bgdog1/3dPrinterCase/Mainboard Mounts for Pro and XL (Same) V5.x Cases/Mainboard Mount XL V5 - SKR V1.X wMounts.stl

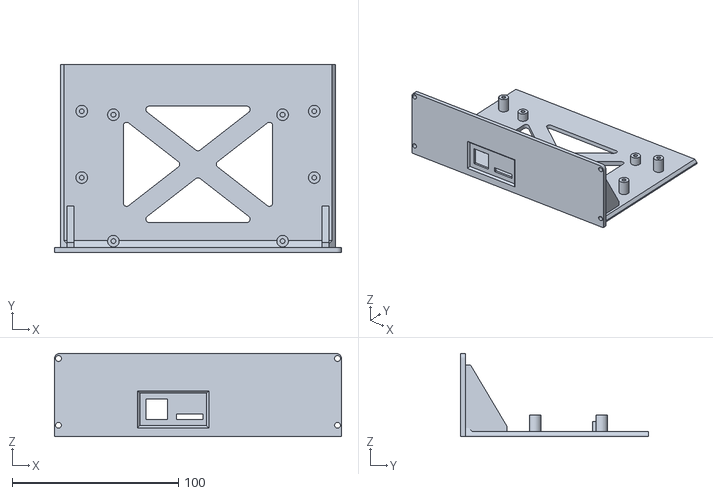
[picture p15: CAD file, 2023-01-29]
Mainboard Mounts for Pro and XL (Same) V5.x Cases/Mainboard Mount XL V5 - SKR V1.X wMounts.stl
172.8 x 113.0 x 50.0
