bgdog1/3dPrinterCase/Mainboard Mounts for V5.x Cases/Mainboard Mount V2 - SKR V1.3 V1.4 V3.0.stl

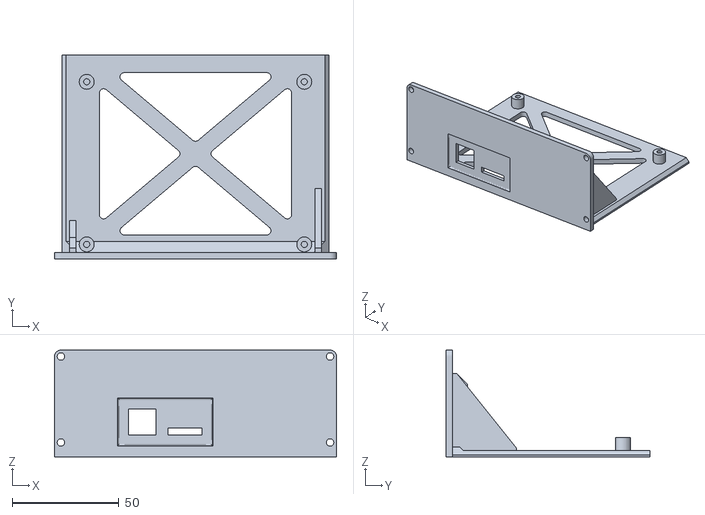
[picture p16: CAD file, 2023-01-29]
Mainboard Mounts for V5.x Cases/Mainboard Mount V2 - SKR V1.3 V1.4 V3.0.stl
132.0 x 95.3 x 50.0
