bgdog1/3dPrinterCase/Rear Mount Ender 3 Case V3.0/E3 Pro Rear Case V5 - Mainboard Lid BTT LOGO.stl

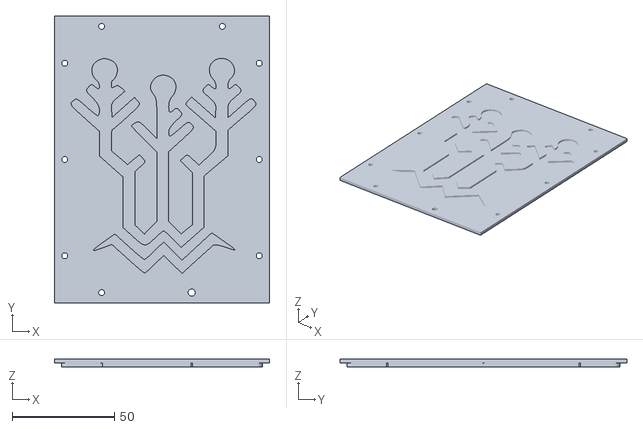
[picture p17: CAD file, 2023-02-08]
Rear Mount Ender 3 Case V3.0/E3 Pro Rear Case V5 - Mainboard Lid BTT LOGO.stl
105.0 x 140.0 x 4.00
