bgdog1/3dPrinterCase/Mainboard Mounts - Case 4.0/Mainboard Mount V4_0 - SKR GTR V1_0.stl

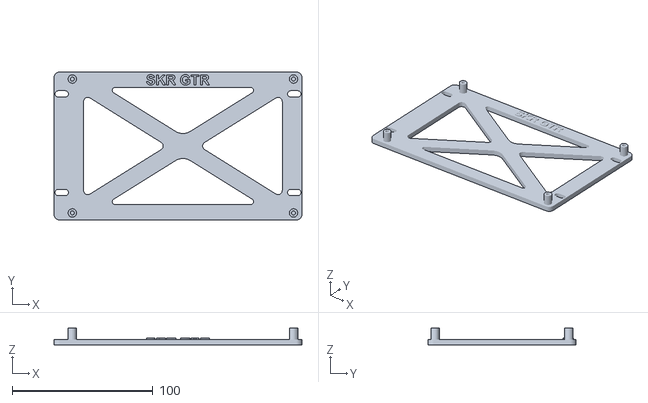
[picture p18: CAD file, 2020-06-05]
Mainboard Mounts - Case 4.0/Mainboard Mount V4_0 - SKR GTR V1_0.stl
176.0 x 105.0 x 12.0
