bgdog1/3dPrinterCase/Mainboard Mounts for Pro and XL (Same) V5.x Cases/Mainboard Mount XL V5 - Duet Wifi.stl

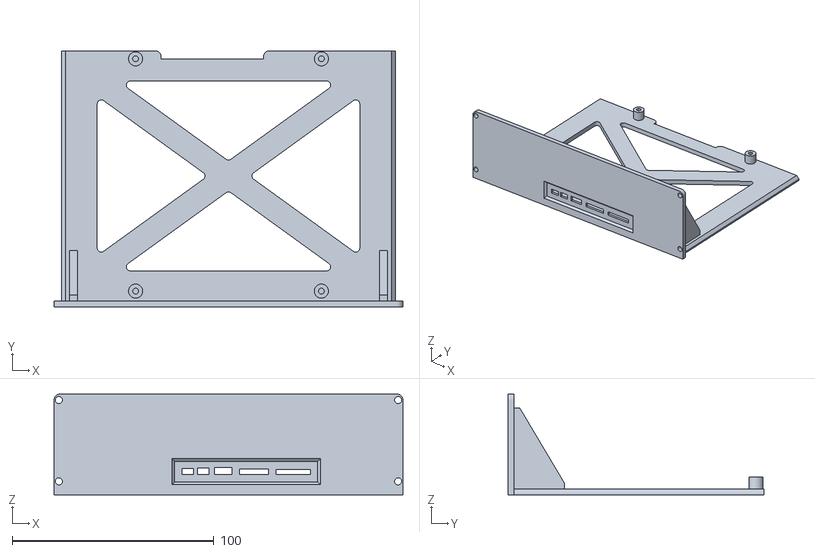
[picture p19: CAD file, 2023-01-29]
Mainboard Mounts for Pro and XL (Same) V5.x Cases/Mainboard Mount XL V5 - Duet Wifi.stl
172.8 x 127.0 x 50.0
