bgdog1/3dPrinterCase/Mainboard Mounts for V5.X Cases/Mainboard Mount V2 - Duet WiFi.stl

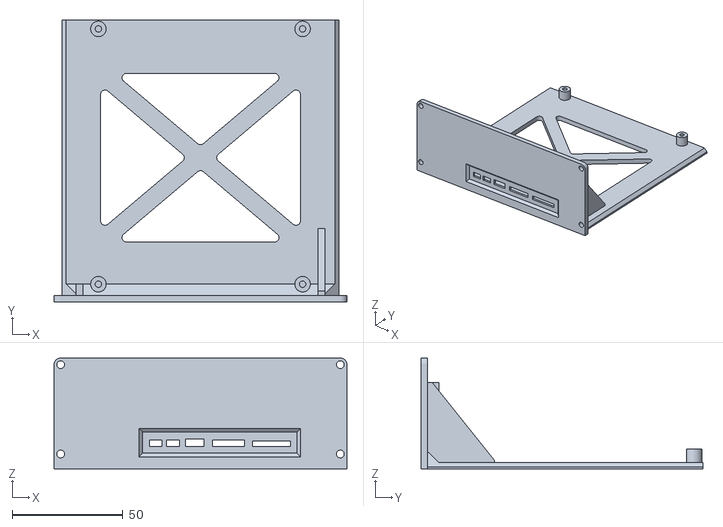
[picture p20: CAD file, 2023-01-29]
Mainboard Mounts for V5.X Cases/Mainboard Mount V2 - Duet WiFi.stl
132.0 x 127.0 x 50.0
