bgdog1/3dPrinterCase/Case - PRO V5.0 - 2 Piece/Main Body Front Pro V5_0 - 2 pc Standard.stl

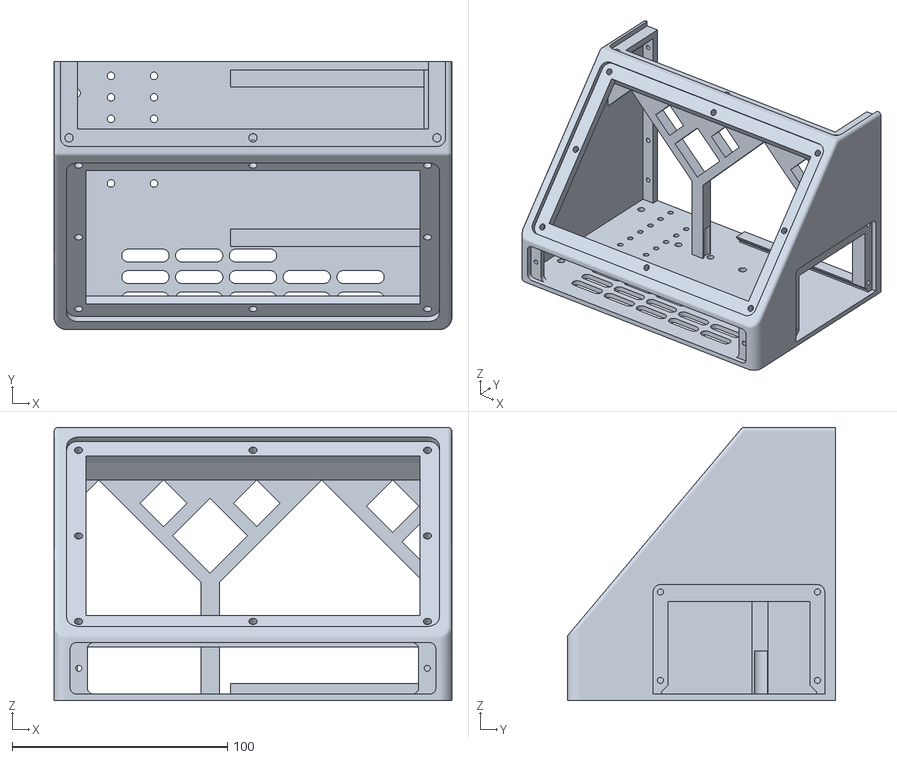
[picture p21: CAD file, 2020-09-07]
Case - PRO V5.0 - 2 Piece/Main Body Front Pro V5_0 - 2 pc Standard.stl
185.0 x 124.8 x 127.0
