bgdog1/3dPrinterCase/Display Mounts - Universal/Display Mount - TFT24V1_1 Main Body SD Accedd.stl

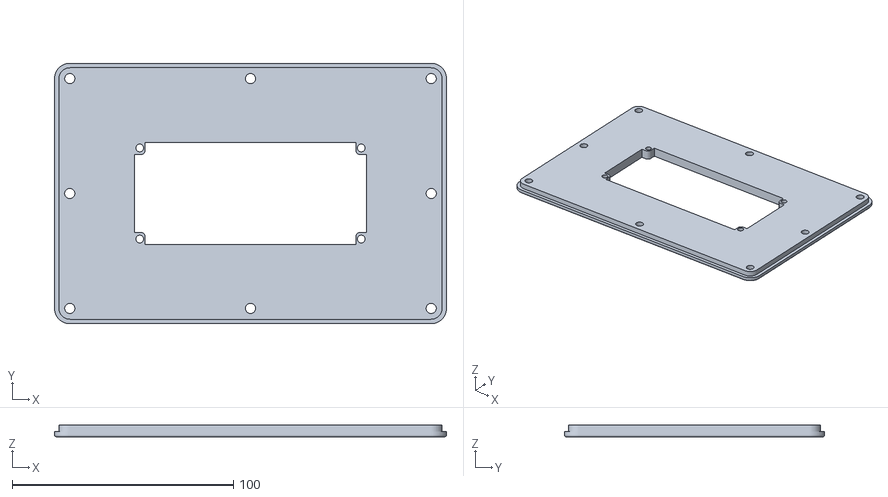
[picture p22: CAD file, 2020-06-08]
Display Mounts - Universal/Display Mount - TFT24V1_1 Main Body SD Accedd.stl
177.1 x 117.6 x 5.40
