bgdog1/3dPrinterCase/Mainboard Mounts for Pro and XL (Same) V5.x Cases/Mainboard Mount XL V5 - SKR GTR V1.0.stl

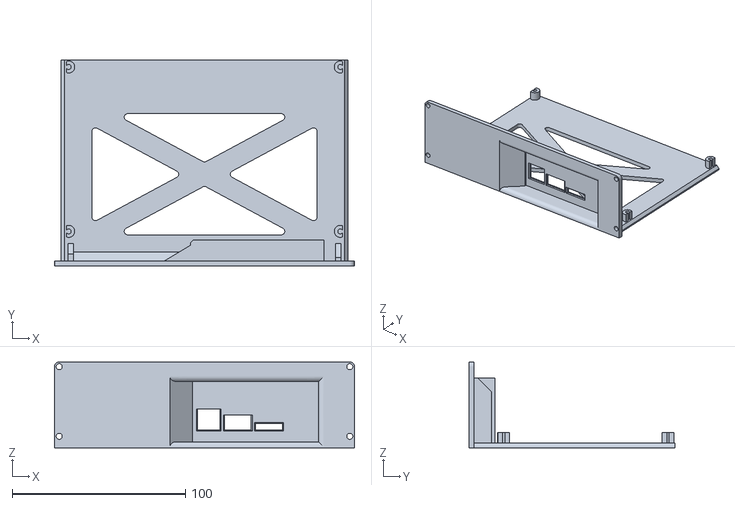
[picture p23: CAD file, 2023-01-29]
Mainboard Mounts for Pro and XL (Same) V5.x Cases/Mainboard Mount XL V5 - SKR GTR V1.0.stl
173.4 x 119.0 x 49.7
