bgdog1/3dPrinterCase/Rear Mount Ender 3 Case V3.0/E3 Pro Rear Case V5 - Mainboard Lid.stl

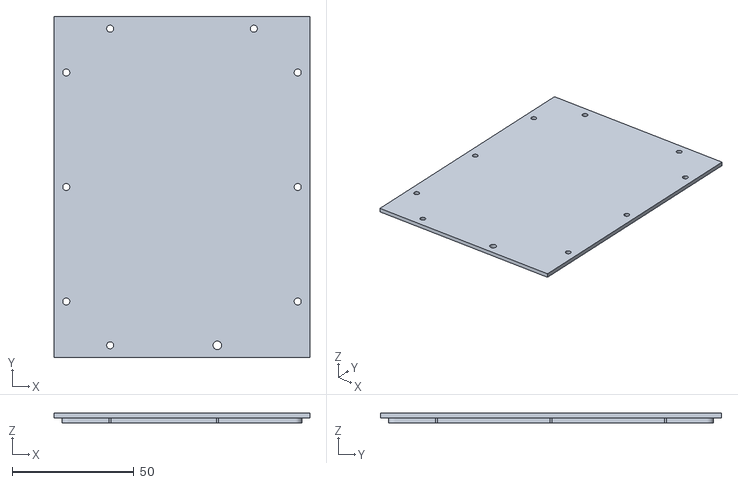
[picture p24: CAD file, 2023-02-08]
Rear Mount Ender 3 Case V3.0/E3 Pro Rear Case V5 - Mainboard Lid.stl
105.0 x 140.0 x 4.00
