bgdog1/3dPrinterCase/Case - PRO V5.0 - 2 Piece/Main Body Rear Pro V5_0 - 2pc Standard.stl

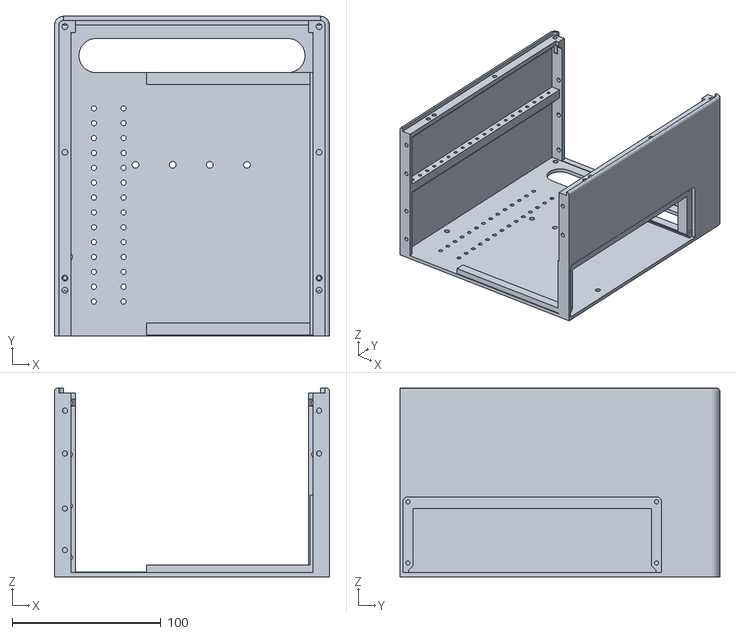
[picture p25: CAD file, 2020-09-07]
Case - PRO V5.0 - 2 Piece/Main Body Rear Pro V5_0 - 2pc Standard.stl
185.0 x 215.0 x 127.0
