bgdog1/3dPrinterCase/Mainboard Mounts for Pro and XL (Same) V5.x Cases/Mainboard Mount XL V5 - SKR Pro V1.1.stl

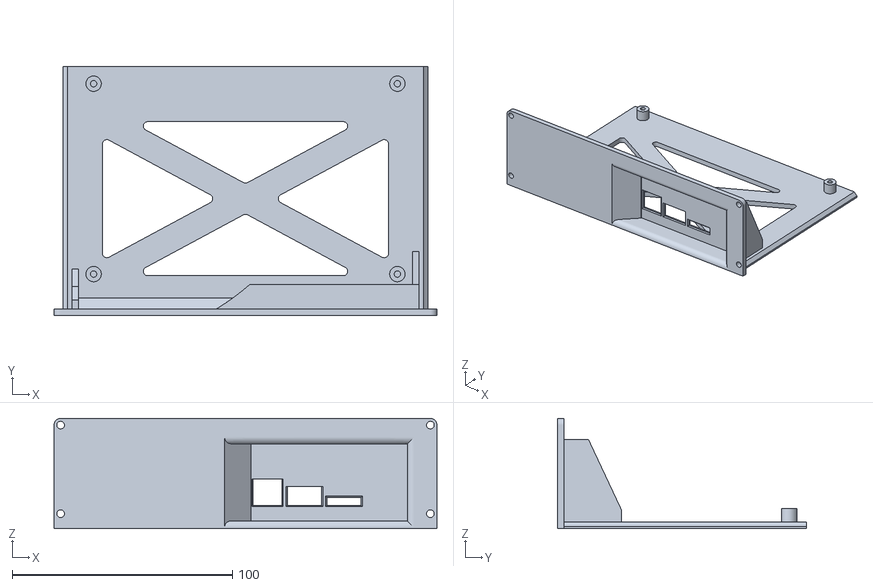
[picture p26: CAD file, 2023-01-29]
Mainboard Mounts for Pro and XL (Same) V5.x Cases/Mainboard Mount XL V5 - SKR Pro V1.1.stl
174.0 x 113.0 x 50.0
