bgdog1/3dPrinterCase/Mainboard Mounts for V5.X Cases/Mainboard Mount V2 - Creality 115_SKR E3.stl

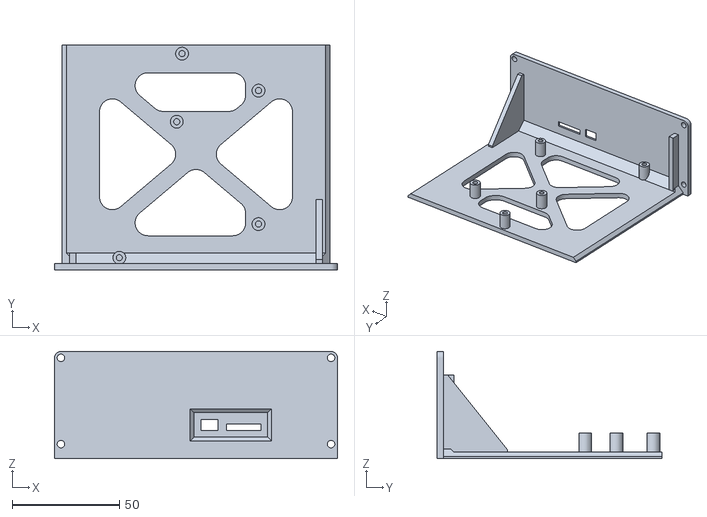
[picture p27: CAD file, 2023-01-29]
Mainboard Mounts for V5.X Cases/Mainboard Mount V2 - Creality 115_SKR E3.stl
132.0 x 105.0 x 50.0
