bgdog1/3dPrinterCase/Mainboard Mounts - Case 4.0/Mainboard Mount V4_0 - Creality 2_X.stl

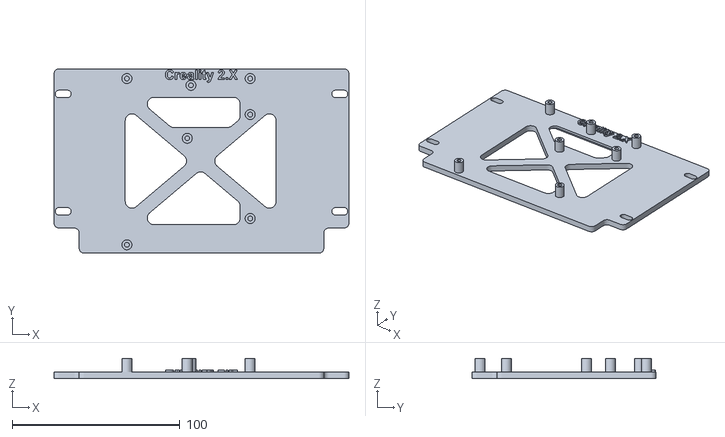
[picture p28: CAD file, 2020-06-01]
Mainboard Mounts - Case 4.0/Mainboard Mount V4_0 - Creality 2_X.stl
176.0 x 110.0 x 12.0
