bgdog1/3dPrinterCase/Mainboard Mounts for Pro and XL (Same) V5.x Cases/Mainboard Mount XL V5 - SKR V1.X wWIFI MOTEXP V1.0.stl

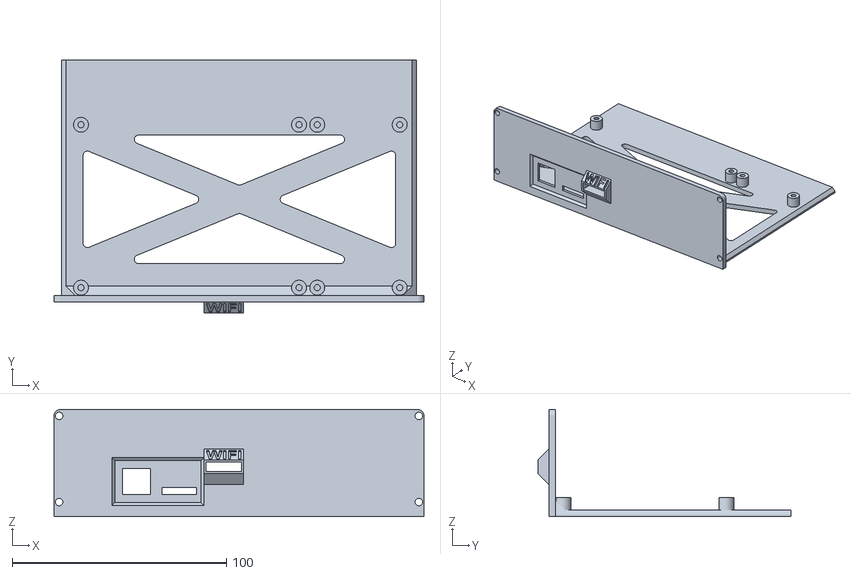
[picture p29: CAD file, 2023-01-29]
Mainboard Mounts for Pro and XL (Same) V5.x Cases/Mainboard Mount XL V5 - SKR V1.X wWIFI MOTEXP V1.0.stl
172.8 x 118.0 x 50.0
