bgdog1/3dPrinterCase/Mainboard Mounts for V5.X Cases/Mainboard Mount V2 - Creality V2_1+.stl

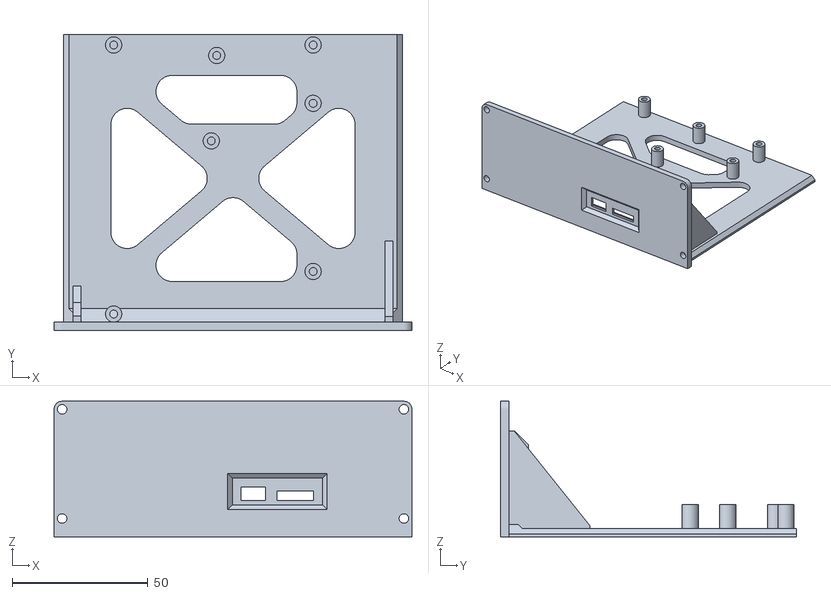
[picture p30: CAD file, 2023-01-29]
Mainboard Mounts for V5.X Cases/Mainboard Mount V2 - Creality V2_1+.stl
132.0 x 109.0 x 50.0
