bgdog1/3dPrinterCase/Rear Mount Ender 3 Case V3.0/E3 Pro Rear Case V5 - 1 Piece Main Body.stl

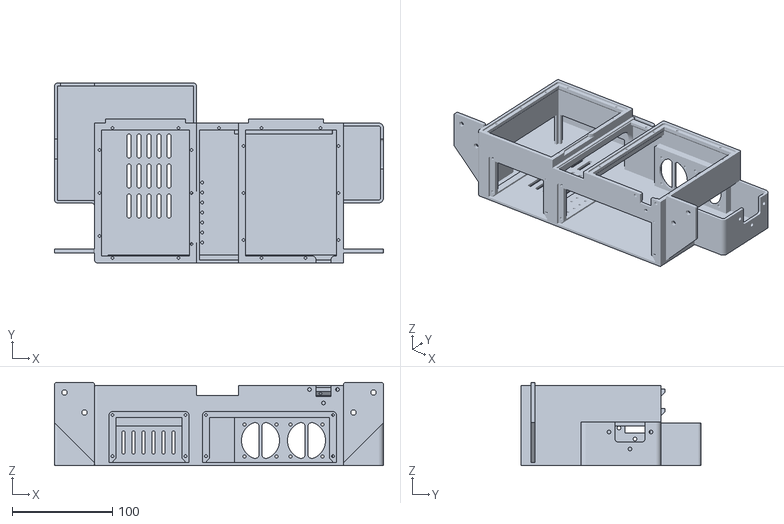
[picture p31: CAD file, 2023-02-08]
Rear Mount Ender 3 Case V3.0/E3 Pro Rear Case V5 - 1 Piece Main Body.stl
329.0 x 180.0 x 83.0
