bgdog1/3dPrinterCase/Mainboard Mounts for V5.X Cases/Mainboard Mount V2 - SKR 1.4 wWIFI.stl

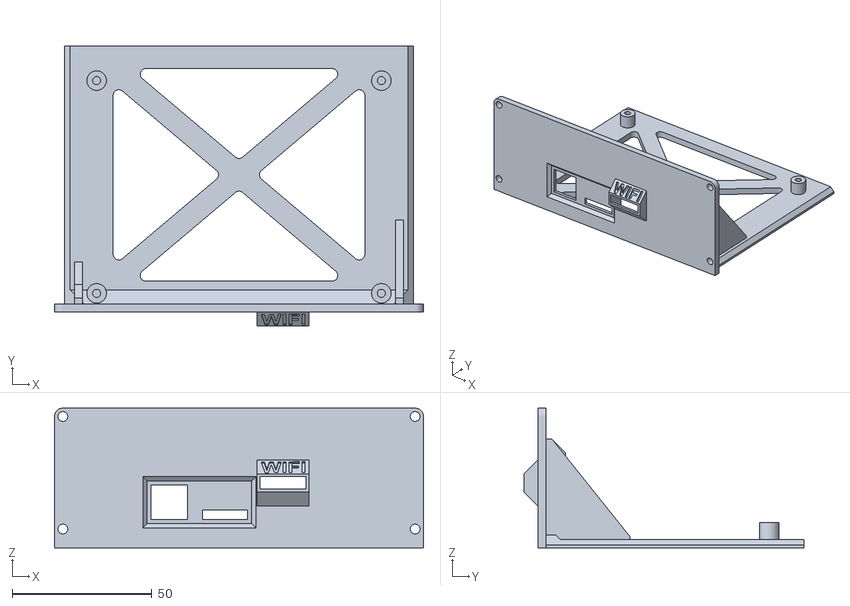
[picture p32: CAD file, 2023-01-29]
Mainboard Mounts for V5.X Cases/Mainboard Mount V2 - SKR 1.4 wWIFI.stl
132.0 x 100.3 x 50.0
