bgdog1/3dPrinterCase/Mainboard Mounts - Case 4.0/Mainboard Mount V4_0 - Blank.stl

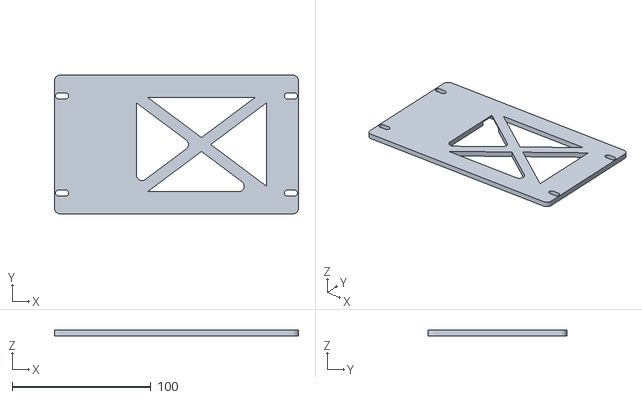
[picture p33: CAD file, 2020-06-01]
Mainboard Mounts - Case 4.0/Mainboard Mount V4_0 - Blank.stl
176.0 x 100.0 x 4.00
