bgdog1/3dPrinterCase/Rear Mount Ender 3 Case V3.0/E3 Pro Rear Case V5 - Mainboard Body.stl

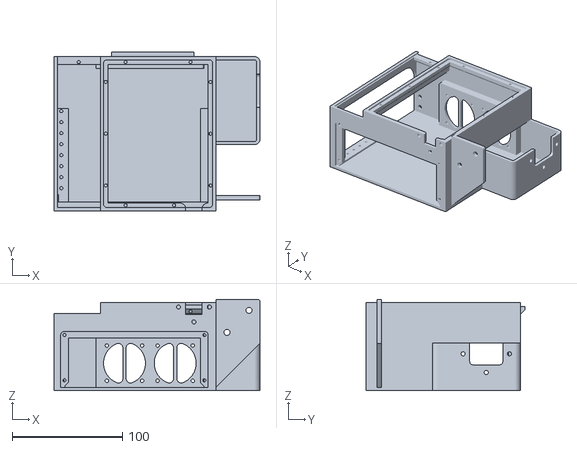
[picture p34: CAD file, 2023-02-07]
Rear Mount Ender 3 Case V3.0/E3 Pro Rear Case V5 - Mainboard Body.stl
187.0 x 144.0 x 83.0
