bgdog1/3dPrinterCase/Mainboard Mounts for V5.X Cases/Mainboard Mount - Creality 115_SKR E3.stl

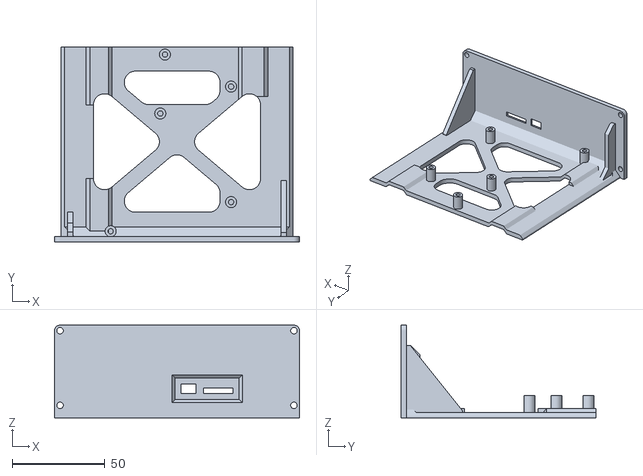
[picture p35: CAD file, 2020-03-22]
Mainboard Mounts for V5.X Cases/Mainboard Mount - Creality 115_SKR E3.stl
132.0 x 105.0 x 50.0
