bgdog1/3dPrinterCase/Mainboard Mounts for V5.X Cases/Mainboard Mount - Creality V2_1+.stl

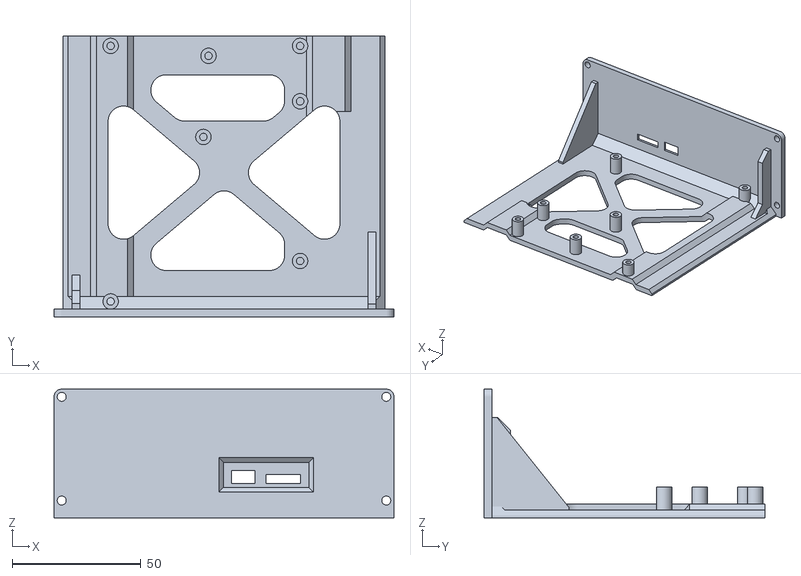
[picture p36: CAD file, 2020-03-22]
Mainboard Mounts for V5.X Cases/Mainboard Mount - Creality V2_1+.stl
132.0 x 109.0 x 50.0
