bgdog1/3dPrinterCase/Buck Converters - Case 3.0 and 5.0/Buck Converter Mount Dbl17x48.stl

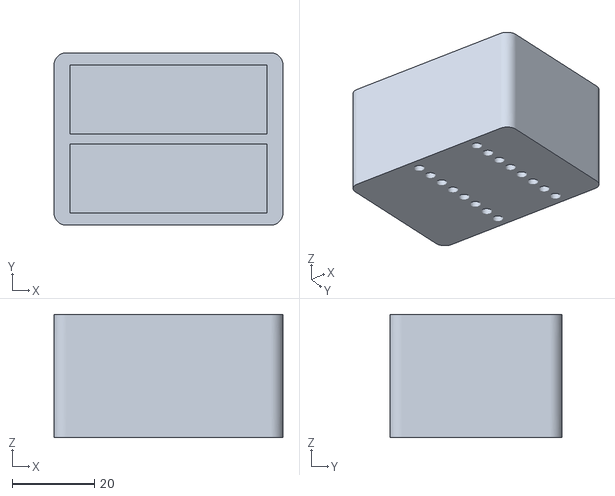
[picture p38: CAD file, 2020-03-22]
Buck Converters - Case 3.0 and 5.0/Buck Converter Mount Dbl17x48.stl
55.8 x 42.0 x 30.0
