bgdog1/3dPrinterCase/Case and Components V4_0 ONLY/RPi Mounts/RPi Mount V4_0 - Horiz_Plain.step

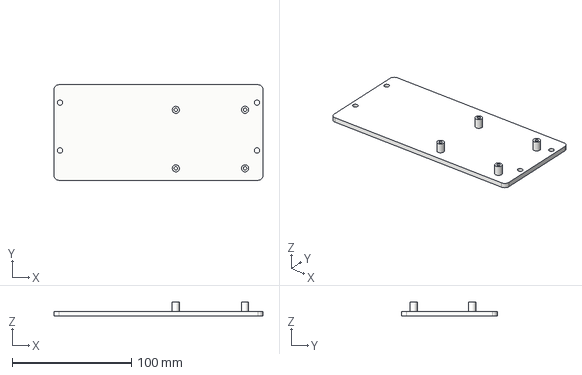
[picture p40: CAD file, 2020-04-26]
Case and Components V4_0 ONLY/RPi Mounts/RPi Mount V4_0 - Horiz_Plain.step
175.0 x 80.0 x 12.0 mm
