bgdog1/3dPrinterCase/CPU Mounts/CPU Mount V2 - Blank.step

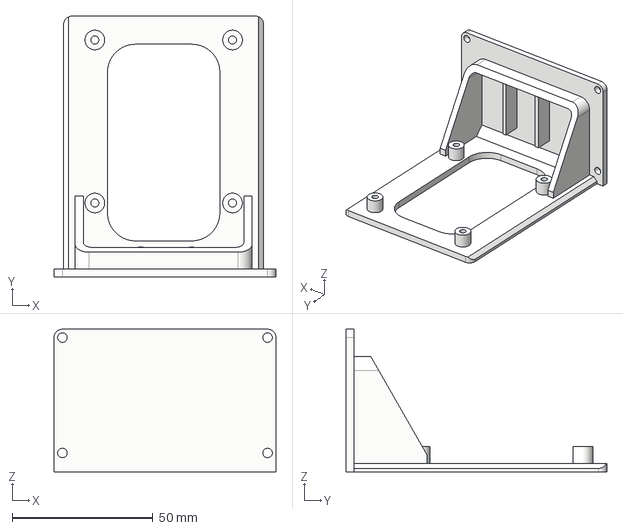
[picture p41: CAD file, 2023-10-05]
CPU Mounts/CPU Mount V2 - Blank.step
79.0 x 92.8 x 50.8 mm
