bgdog1/3dPrinterCase/Display Mounts - Universal/Display Mount - TFT35V20.step

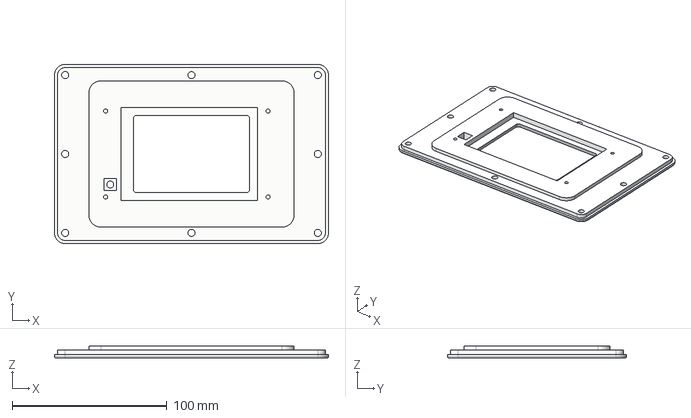
[picture p42: CAD file, 2020-08-09]
Display Mounts - Universal/Display Mount - TFT35V20.step
177.1 x 115.8 x 8.00 mm
