bgdog1/3dPrinterCase/Display Mounts/Display Mount - TFT50V30 Cover.stl

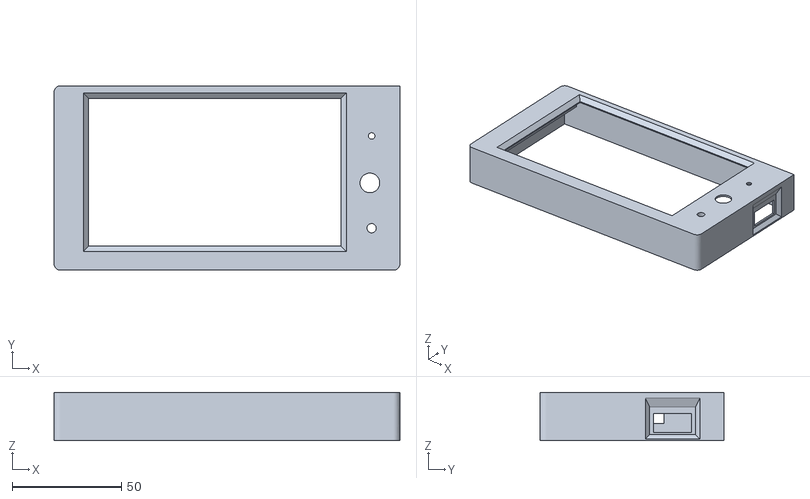
[picture p43: CAD file, 2020-12-30]
Display Mounts/Display Mount - TFT50V30 Cover.stl
158.5 x 84.5 x 22.2
