bgdog1/3dPrinterCase/Fan Hats - Case 3.0 and 5.0/Dual 4020 Fan Hat - Mounting Base.stl

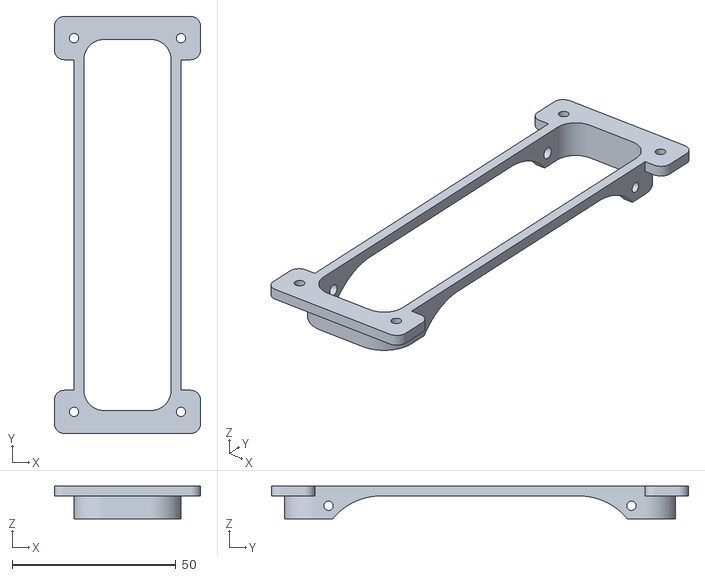
[picture p44: CAD file, 2020-04-03]
Fan Hats - Case 3.0 and 5.0/Dual 4020 Fan Hat - Mounting Base.stl
44.6 x 127.2 x 10.0
