bgdog1/3dPrinterCase/Fan Mounts - Case 3.0 and 5.0/Fan Mount - 4020mm DWT + Bucks + Acc.stl

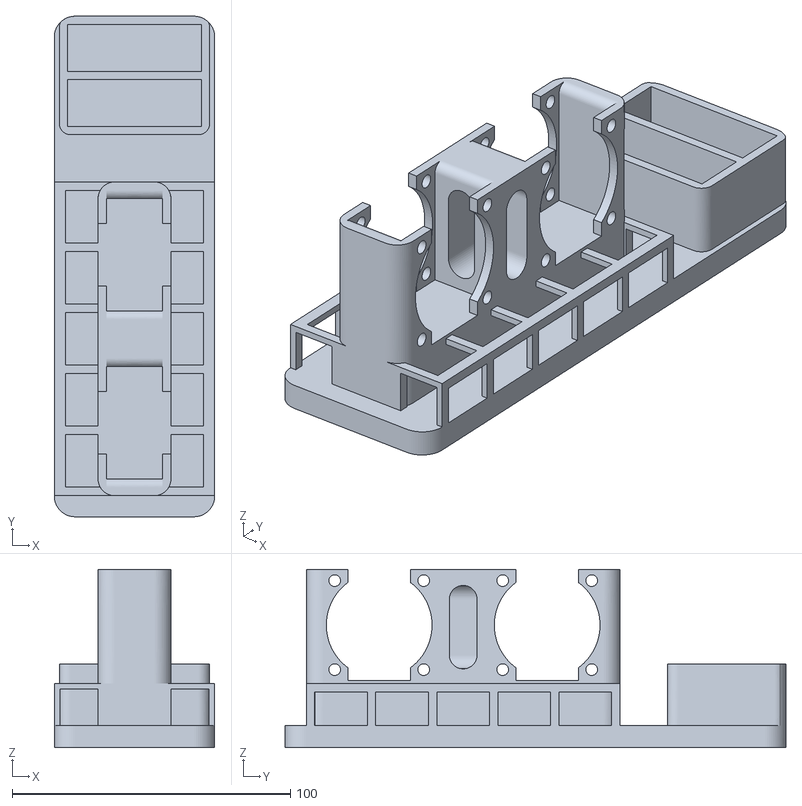
[picture p45: CAD file, 2020-03-30]
Fan Mounts - Case 3.0 and 5.0/Fan Mount - 4020mm DWT + Bucks + Acc.stl
57.7 x 180.0 x 64.0
