bgdog1/3dPrinterCase/Fan Mounts _ Case 3.0 and 5.0/Rear Fan Mount - External 100x25mm Cover.stl

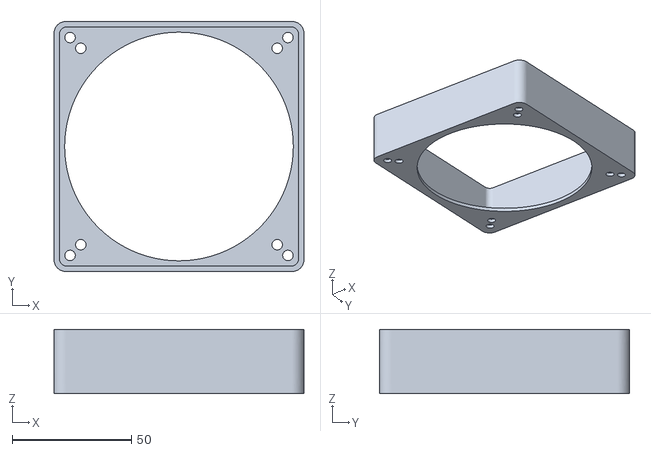
[picture p46: CAD file, 2020-03-28]
Fan Mounts _ Case 3.0 and 5.0/Rear Fan Mount - External 100x25mm Cover.stl
105.0 x 105.0 x 26.9
