bgdog1/3dPrinterCase/Front Covers ALL/Front Vent -  Blank.step

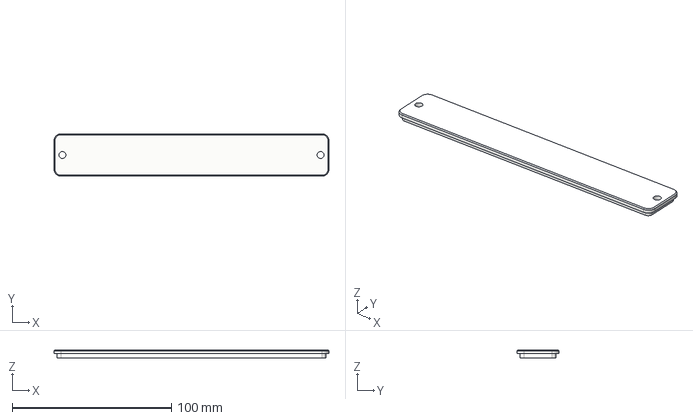
[picture p47: CAD file, 2020-04-05]
Front Covers ALL/Front Vent - Blank.step
172.6 x 26.6 x 5.20 mm
