bgdog1/3dPrinterCase/Front Vents - Universal/Front Vent -  SD_Card.stl

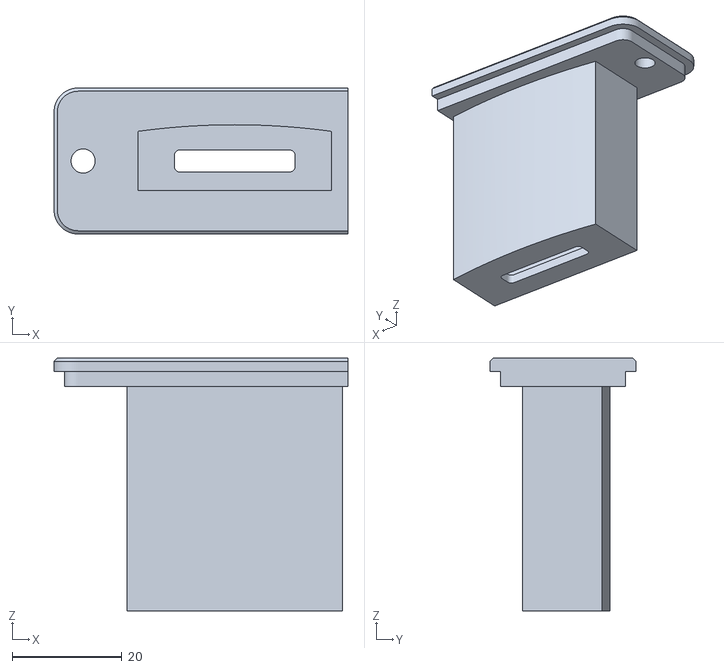
[picture p48: CAD file, 2020-04-26]
Front Vents - Universal/Front Vent - SD_Card.stl
53.5 x 26.6 x 46.0
