bgdog1/3dPrinterCase/Front Vents XL/Front Vent XL - Blank.stl

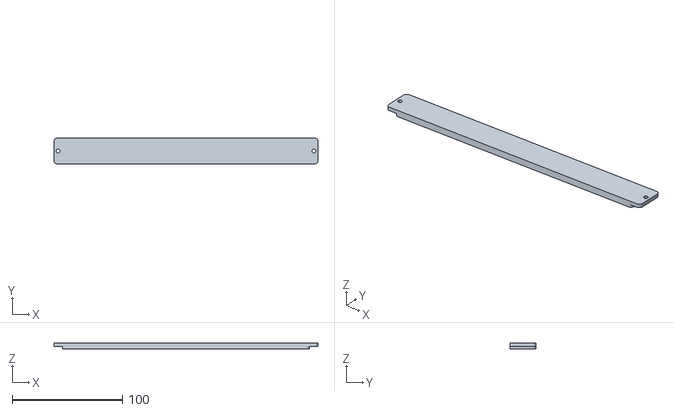
[picture p49: CAD file, 2020-09-06]
Front Vents XL/Front Vent XL - Blank.stl
239.4 x 23.7 x 5.40
