bgdog1/3dPrinterCase/Mainboard Mounts for V5.x Cases/MMV3 CV5 - SKR V3EZ.stl

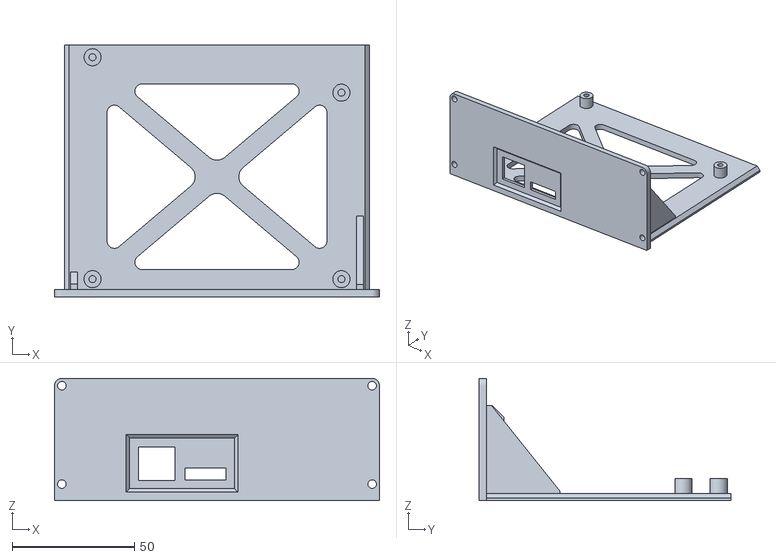
[picture p50: CAD file, 2023-08-20]
Mainboard Mounts for V5.x Cases/MMV3 CV5 - SKR V3EZ.stl
133.0 x 103.0 x 50.0
