bgdog1/3dPrinterCase/Power Panels - Case 3.0/Power Mount Panel Compact - BLANK.stl

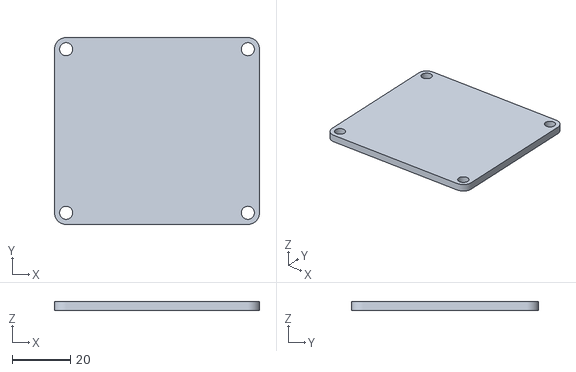
[picture p51: CAD file, 2020-03-22]
Power Panels - Case 3.0/Power Mount Panel Compact - BLANK.stl
70.5 x 64.2 x 3.00
