bgdog1/3dPrinterCase/Rear Fan Cover/Rear Fan External Cover 92mm.stl

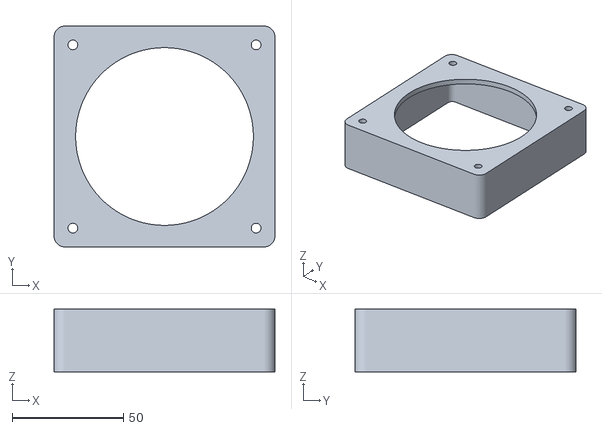
[picture p52: CAD file, 2021-01-09]
Rear Fan Cover/Rear Fan External Cover 92mm.stl
99.5 x 99.5 x 28.2
