bgdog1/3dPrinterCase/Rear Mount Ender 3 Case V3.0/E3 Rear Case V5 - MB Wire Chute.stl

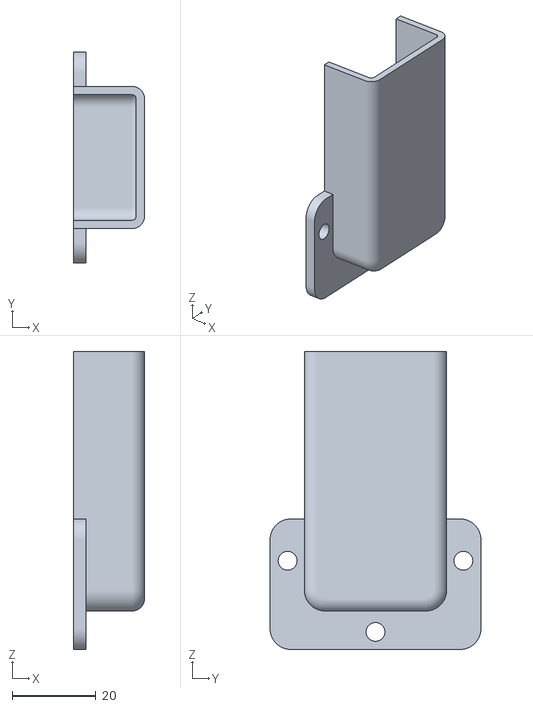
[picture p53: CAD file, 2023-02-08]
Rear Mount Ender 3 Case V3.0/E3 Rear Case V5 - MB Wire Chute.stl
17.0 x 50.4 x 71.2
