bgdog1/3dPrinterCase/Rear Panel XL/Rear Panel - BLANK.stl

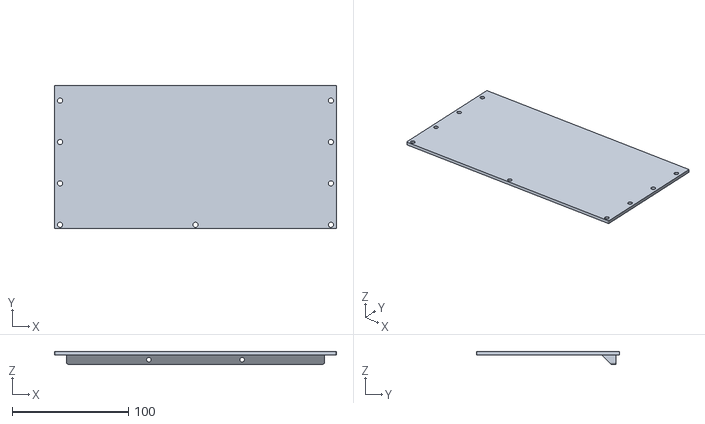
[picture p54: CAD file, 2020-09-12]
Rear Panel XL/Rear Panel - BLANK.stl
242.6 x 123.4 x 11.0
