bgdog1/3dPrinterCase/Rear Panels - Case 4.0 and up/Rear Panel - CR10_100mm_RJ45_2USB.stl

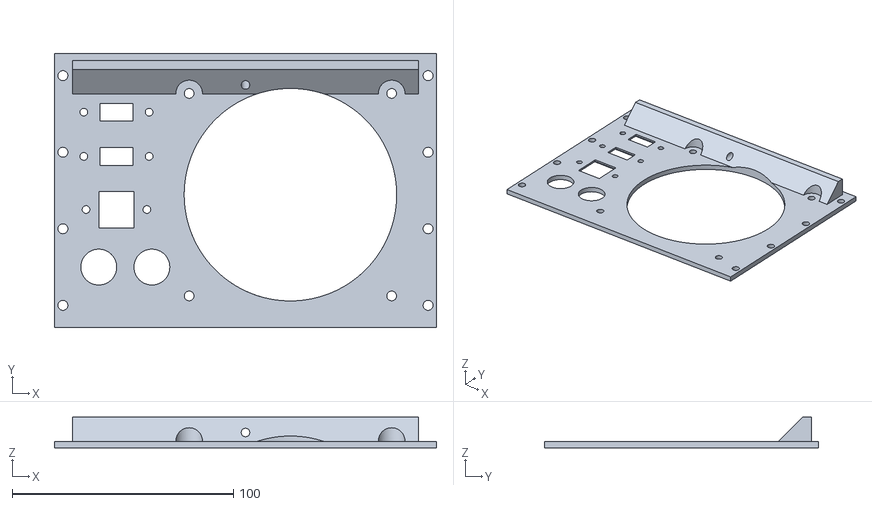
[picture p55: CAD file, 2020-04-26]
Rear Panels - Case 4.0 and up/Rear Panel - CR10_100mm_RJ45_2USB.stl
172.6 x 123.8 x 14.0
