bgdog1/3dPrinterCase/Rear Panels/Rear Panel - 92mmFan and cable holes.stl

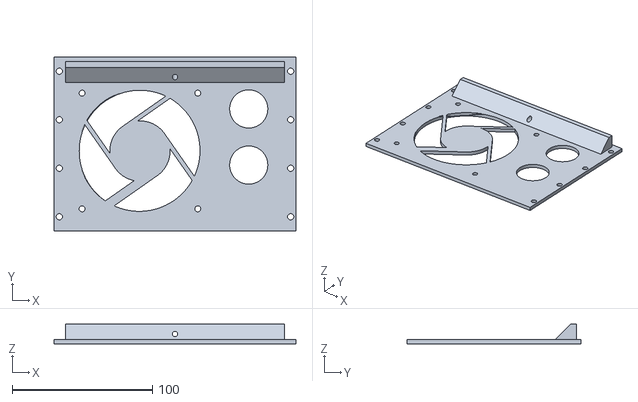
[picture p56: CAD file, 2023-04-07]
Rear Panels/Rear Panel - 92mmFan and cable holes.stl
172.6 x 123.8 x 14.0
