bgdog1/3dPrinterCase/RPi Screen Mounts/TFT 5in RPi Screen Cover.stl

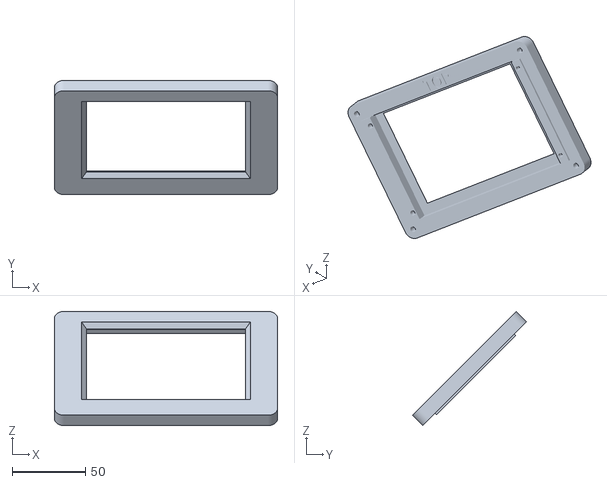
[picture p57: CAD file, 2021-05-05]
RPi Screen Mounts/TFT 5in RPi Screen Cover.stl
152.0 x 77.8 x 77.8
