bgdog1/3dPrinterCase/Side Vent Case 3.0/Side Cover - Blank.stl

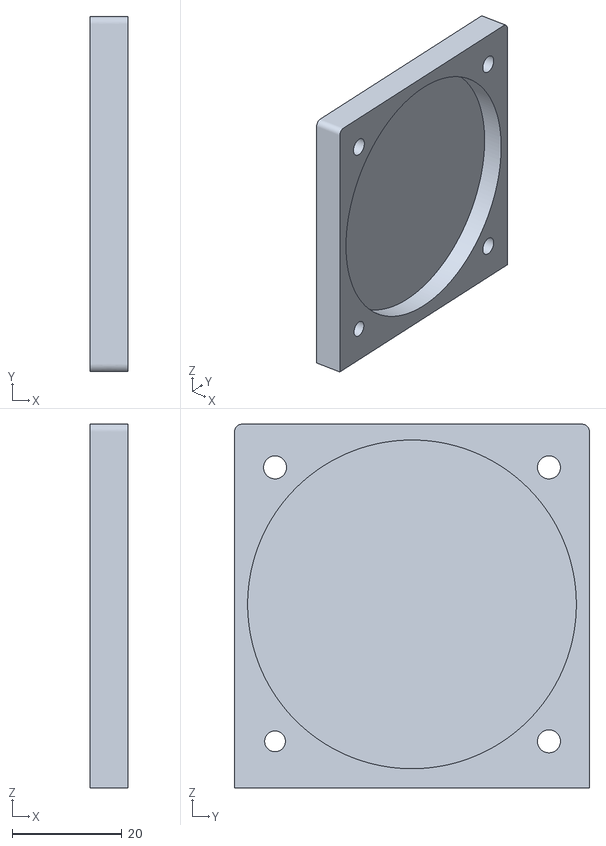
[picture p58: CAD file, 2020-04-05]
Side Vent Case 3.0/Side Cover - Blank.stl
7.00 x 64.8 x 66.4
