bgdog1/3dPrinterCase/Upper Level Mounts - Case 4.0 and up/Upper Level Mount - Wide_2Buck.stl

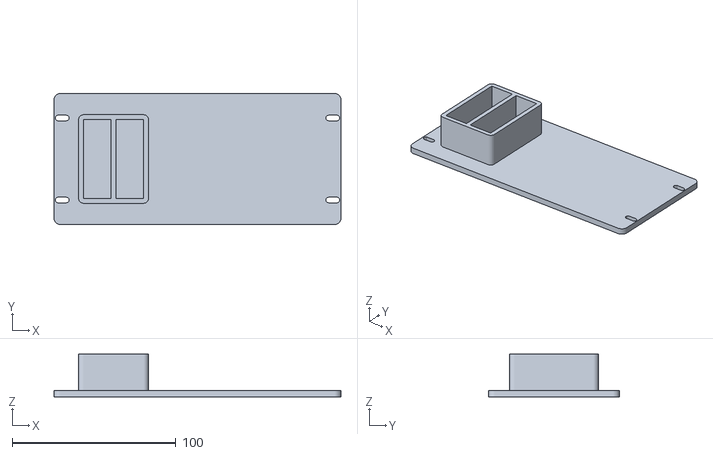
[picture p59: CAD file, 2020-06-04]
Upper Level Mounts - Case 4.0 and up/Upper Level Mount - Wide_2Buck.stl
175.0 x 80.0 x 26.0
