bgdog1/3dPrinterCase/XL and Pro Case Files/Files for Pro V3.0 Only/Power Panel Pro Compact - BLANK.step

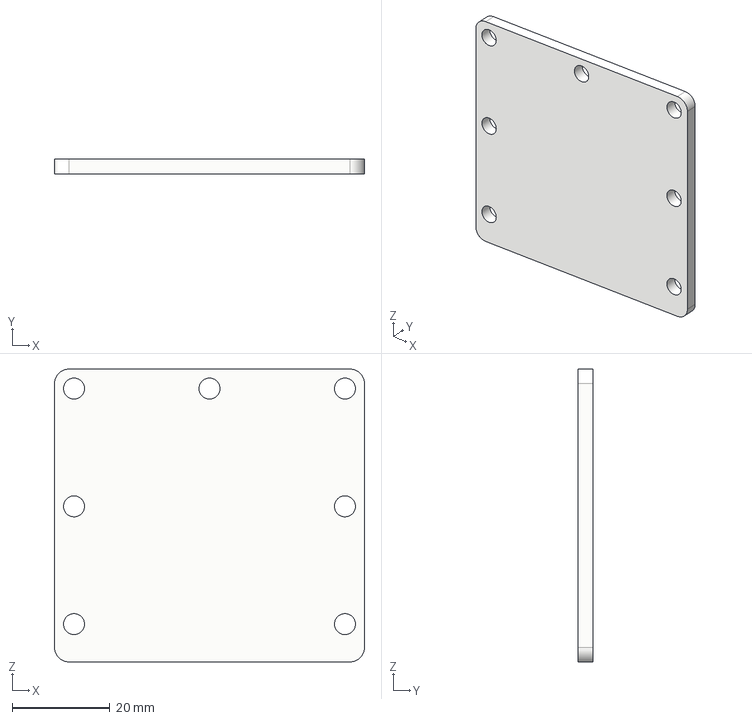
[picture p60: CAD file, 2020-04-22]
XL and Pro Case Files/Files for Pro V3.0 Only/Power Panel Pro Compact - BLANK.step
63.5 x 3.00 x 60.0 mm
