bgdog1/3dPrinterCase/Case - PRO V5.0 - 2 Piece/Base Stand Pro Rear V5_0 Pro_2pc.stl

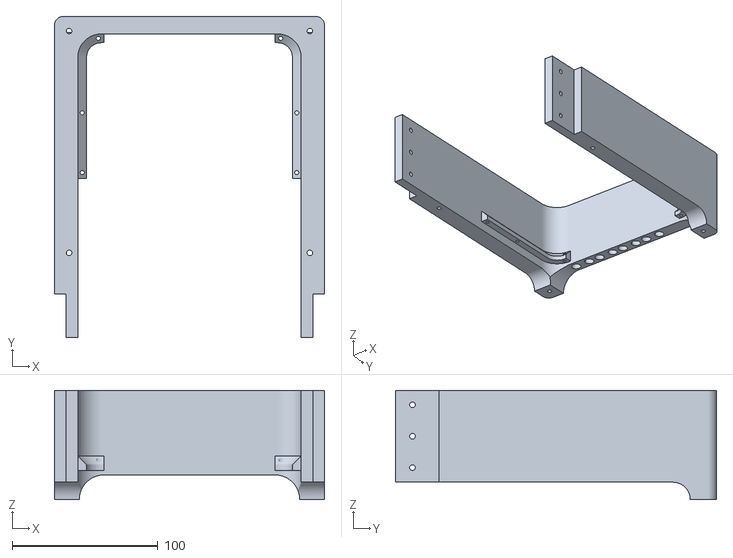
[picture p63: CAD file, 2023-05-02]
Case - PRO V5.0 - 2 Piece/Base Stand Pro Rear V5_0 Pro_2pc.stl
185.0 x 220.0 x 75.0
