bgdog1/3dPrinterCase/Case - PRO V5.0/Base Stand Pro - wSwitch and IEC.stl

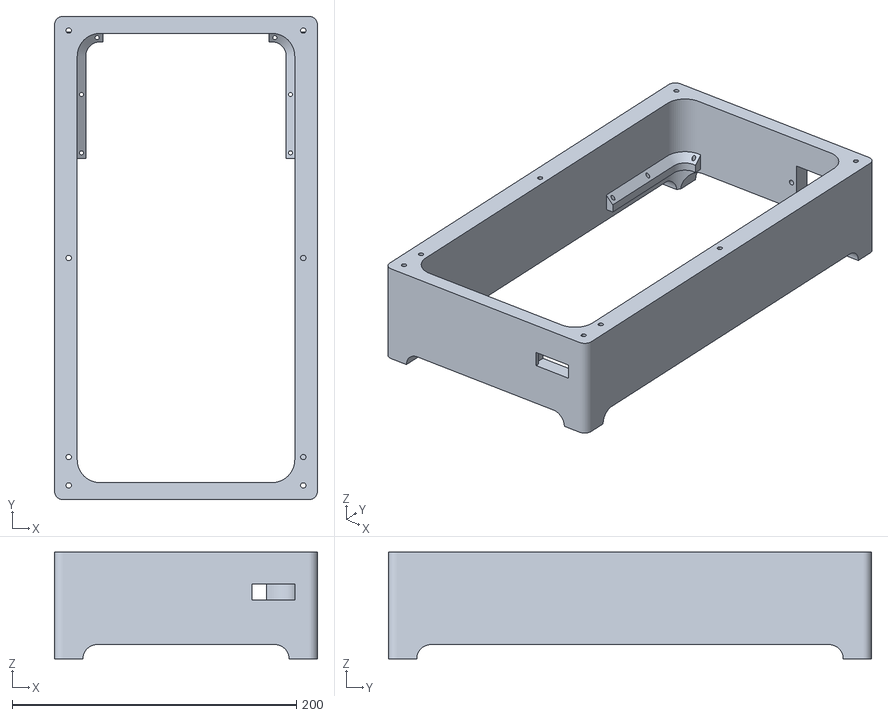
[picture p64: CAD file, 2020-09-22]
Case - PRO V5.0/Base Stand Pro - wSwitch and IEC.stl
185.0 x 340.0 x 75.0
