bgdog1/3dPrinterCase/Case - XL Compact V5.X/Lid XL Compact.stl

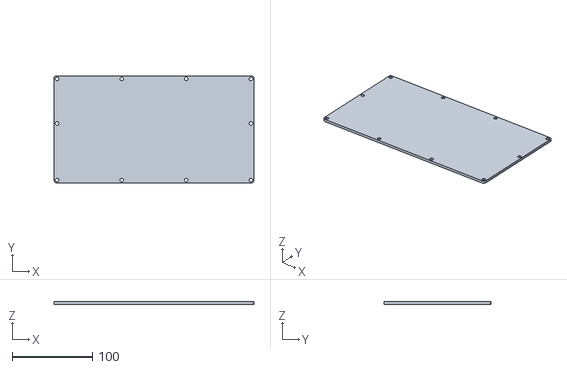
[picture p65: CAD file, 2020-09-06]
Case - XL Compact V5.X/Lid XL Compact.stl
248.5 x 133.1 x 3.20
