bgdog1/3dPrinterCase/Case - XL V5.X/Fan Mount - 4020mm DWT EXTRA Wide.stl

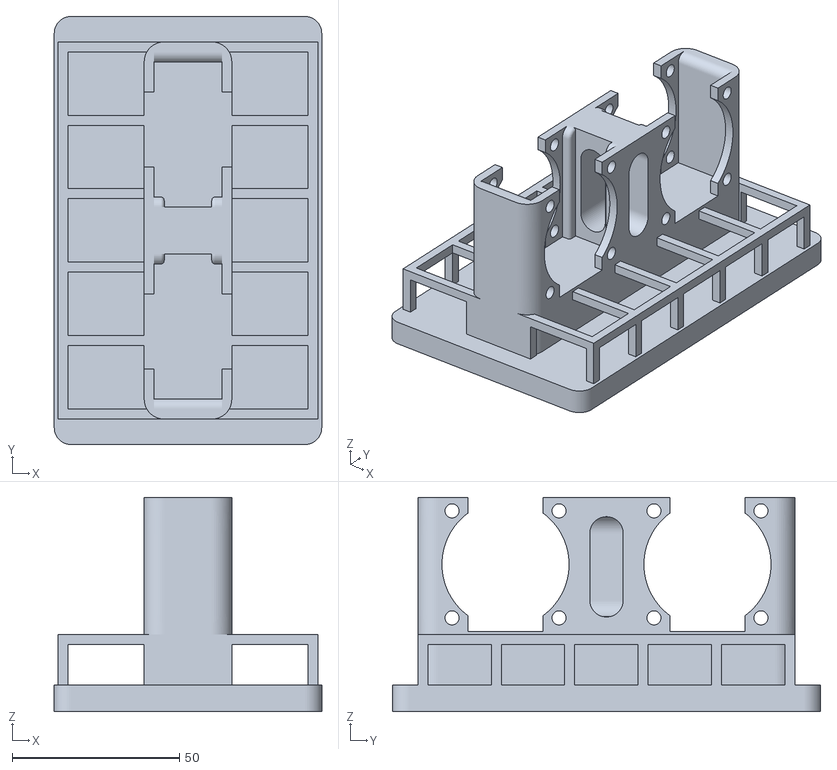
[picture p66: CAD file, 2020-09-22]
Case - XL V5.X/Fan Mount - 4020mm DWT EXTRA Wide.stl
80.0 x 128.0 x 64.0
