bgdog1/3dPrinterCase/CPU Mounts/CPU Mount - RPi 3B+ PRO case.stl

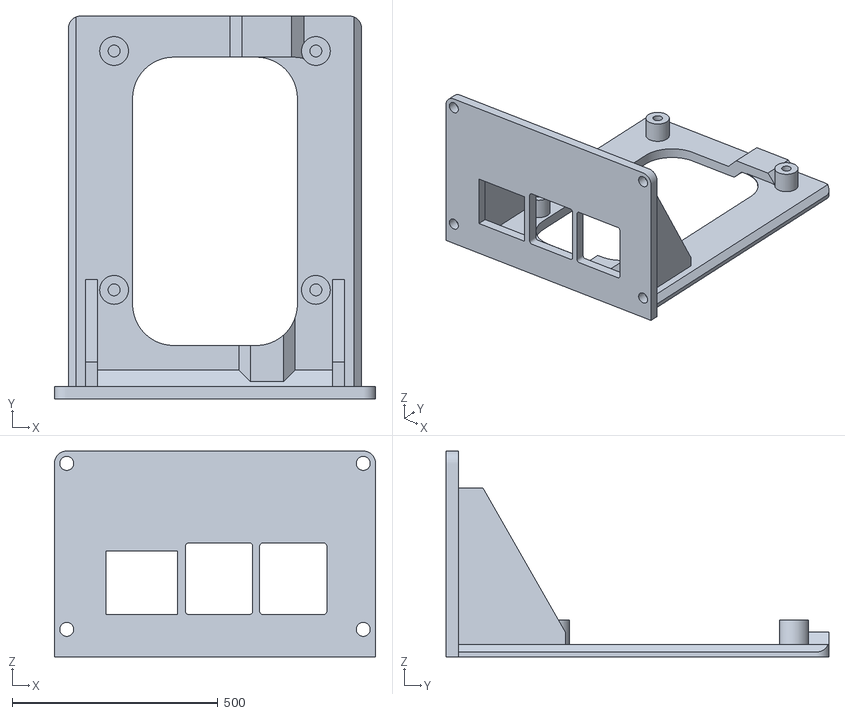
[picture p67: CAD file, 2023-04-07]
CPU Mounts/CPU Mount - RPi 3B+ PRO case.stl
780.0 x 930.0 x 500.0
