bgdog1/3dPrinterCase/Fan Hats - Case 3.0 and 5.0/Dual 4020 Fan Hat - BLANK.stl

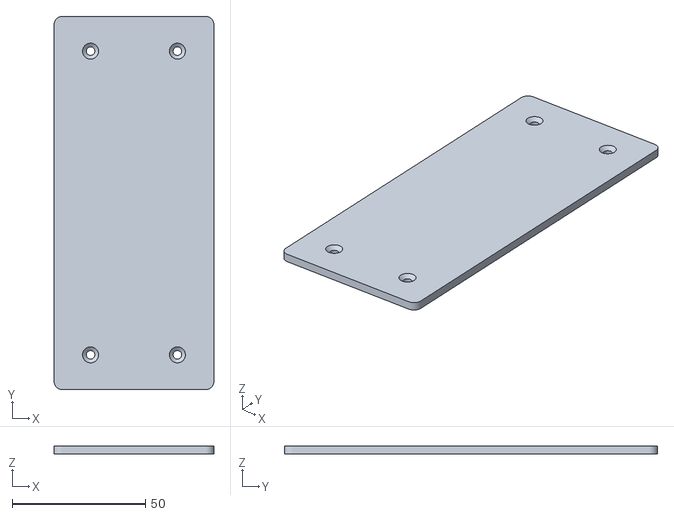
[picture p68: CAD file, 2020-04-03]
Fan Hats - Case 3.0 and 5.0/Dual 4020 Fan Hat - BLANK.stl
60.0 x 140.0 x 3.00
