bgdog1/3dPrinterCase/Fan Mounts - Case 3.0 and 5.0/Fan Mount - Dual 40mm wSgl Cable Tray.stl

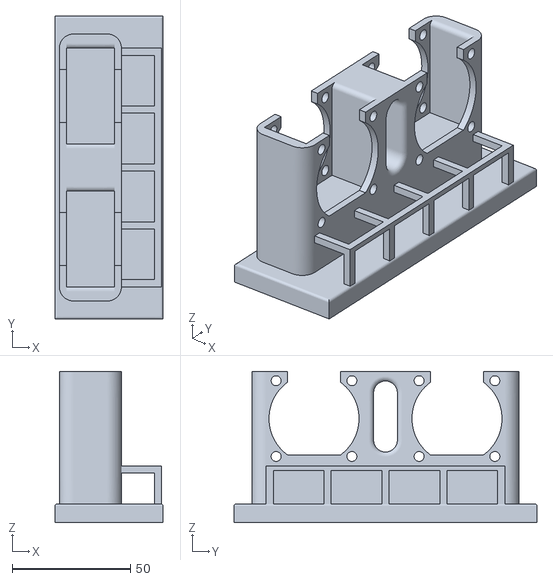
[picture p69: CAD file, 2020-03-29]
Fan Mounts - Case 3.0 and 5.0/Fan Mount - Dual 40mm wSgl Cable Tray.stl
45.7 x 128.0 x 64.0
