bgdog1/3dPrinterCase/Front Vents - Universal/Front Vent -  Hexagon.stl

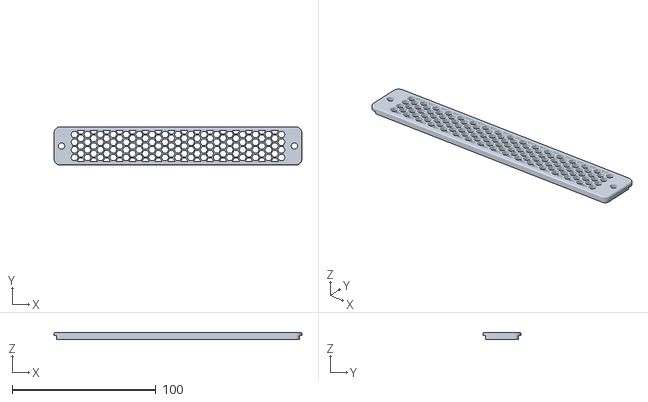
[picture p70: CAD file, 2020-04-05]
Front Vents - Universal/Front Vent - Hexagon.stl
172.6 x 26.6 x 5.20
