bgdog1/3dPrinterCase/Front Vents XL/Front Vent XL - BTT Slots.stl

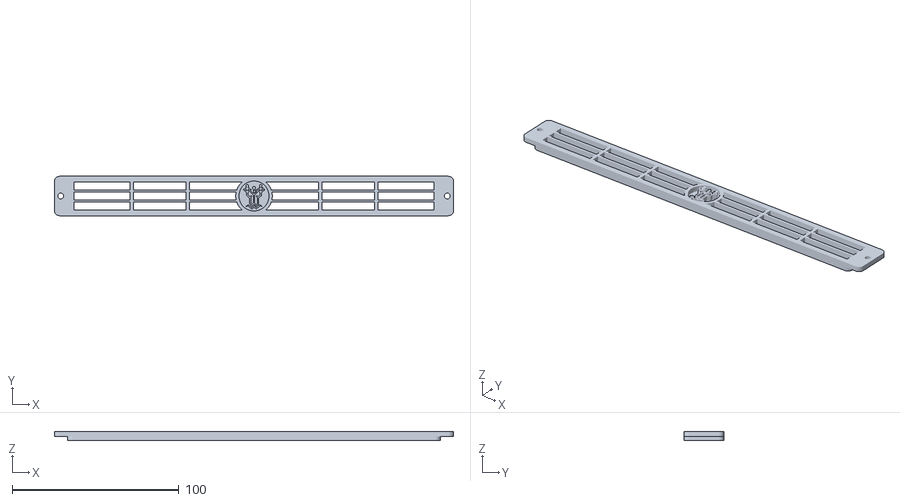
[picture p71: CAD file, 2020-09-06]
Front Vents XL/Front Vent XL - BTT Slots.stl
239.4 x 23.7 x 5.40
