bgdog1/3dPrinterCase/Power Panels - Case 3.0/Power Mount Panel - IEC Connector CR10.stl

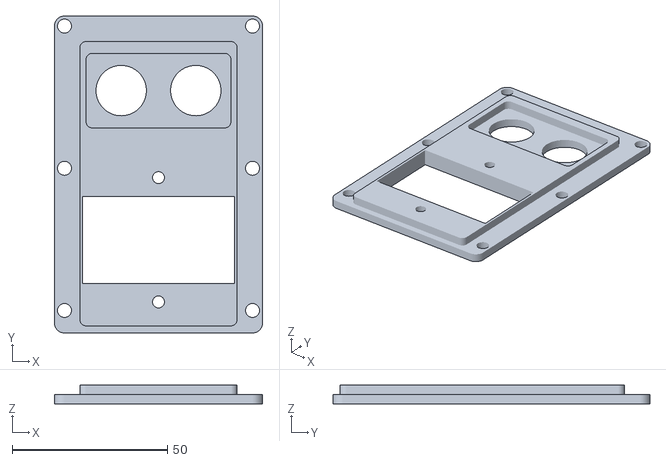
[picture p72: CAD file, 2020-03-22]
Power Panels - Case 3.0/Power Mount Panel - IEC Connector CR10.stl
67.0 x 102.0 x 6.00
