bgdog1/3dPrinterCase/Rear Mount Ender 3 Case V3.0/E3 Rear Case V5 - CPU Side Wire Chute.stl

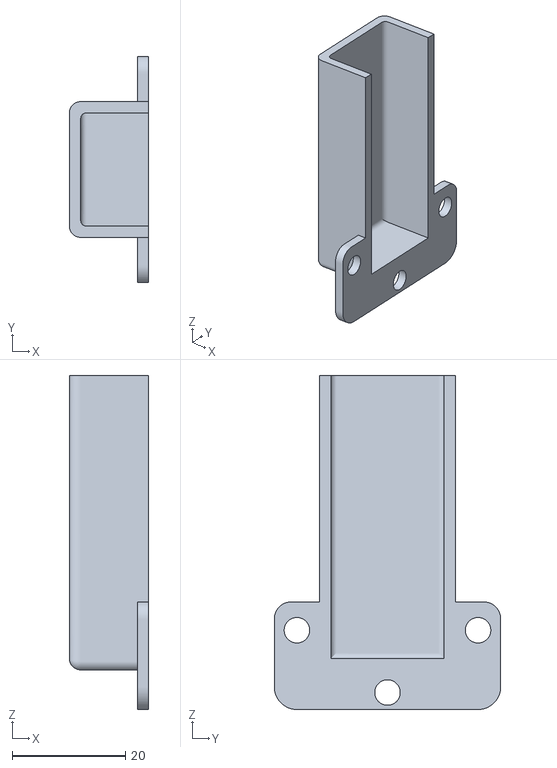
[picture p73: CAD file, 2023-02-08]
Rear Mount Ender 3 Case V3.0/E3 Rear Case V5 - CPU Side Wire Chute.stl
14.0 x 40.0 x 59.0
