bgdog1/3dPrinterCase/Rear Panel XL/Rear Panel - 100mm Fan Left.stl

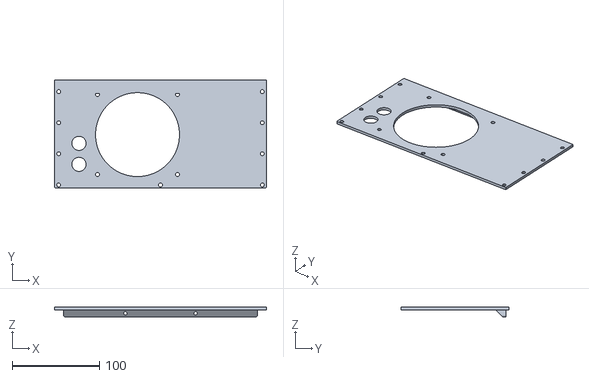
[picture p74: CAD file, 2020-09-12]
Rear Panel XL/Rear Panel - 100mm Fan Left.stl
242.6 x 123.4 x 11.0
