bgdog1/3dPrinterCase/Rear Panels - Case 4.0 and up/Rear Panel - Blank.step

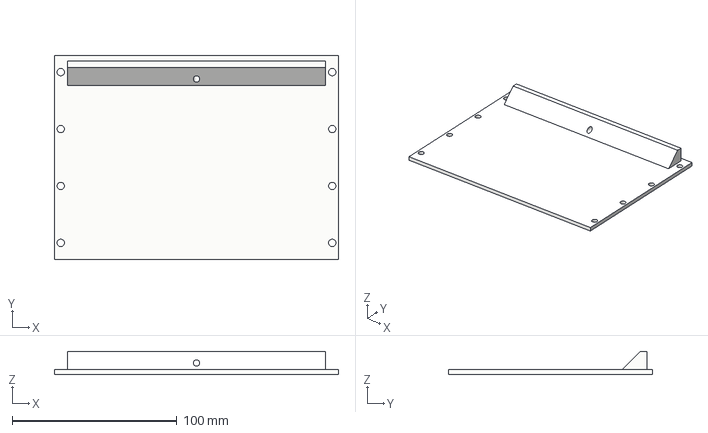
[picture p75: CAD file, 2020-04-24]
Rear Panels - Case 4.0 and up/Rear Panel - Blank.step
172.6 x 123.8 x 14.0 mm
