bgdog1/3dPrinterCase/Rear Panels/Rear Panel - 92mm fan cable and power holes.stl

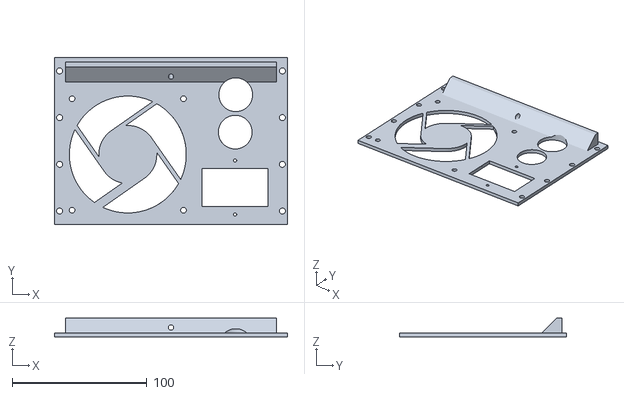
[picture p76: CAD file, 2023-04-07]
Rear Panels/Rear Panel - 92mm fan cable and power holes.stl
172.6 x 123.8 x 14.0
