bgdog1/3dPrinterCase/RPi Screen Mounts/TFT 5in RPi Screen Mount.stl

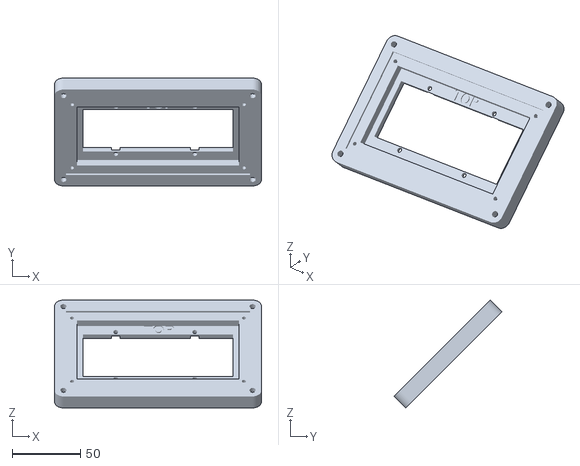
[picture p77: CAD file, 2021-05-05]
RPi Screen Mounts/TFT 5in RPi Screen Mount.stl
152.0 x 79.2 x 79.2
