bgdog1/3dPrinterCase/Upper Level Mounts - Case 4.0 and up/Upper Level Mount - SSR_2.stl

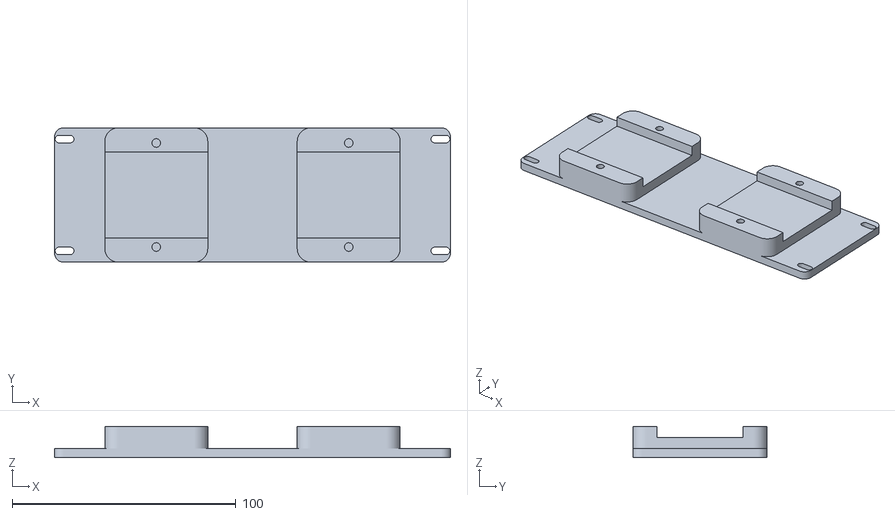
[picture p79: CAD file, 2020-06-04]
Upper Level Mounts - Case 4.0 and up/Upper Level Mount - SSR_2.stl
177.0 x 60.0 x 14.0
