bgdog1/3dPrinterCase/XL and Pro Case Files/Files for Pro V3.0 Only/Lid Pro - Compact.step

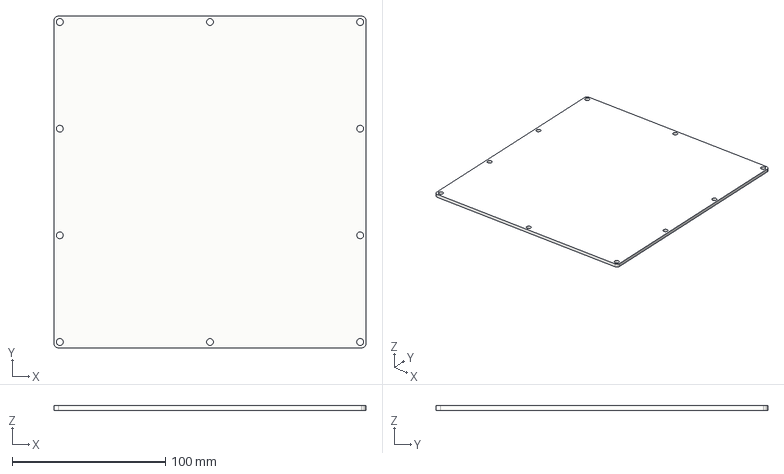
[picture p80: CAD file, 2020-04-10]
XL and Pro Case Files/Files for Pro V3.0 Only/Lid Pro - Compact.step
203.6 x 216.4 x 3.00 mm
