bgdog1/3dPrinterCase/Base Stand - Case 3.0 and 5.0/Base Stand Rear V3_0 Standard_Tall_2pc.stl

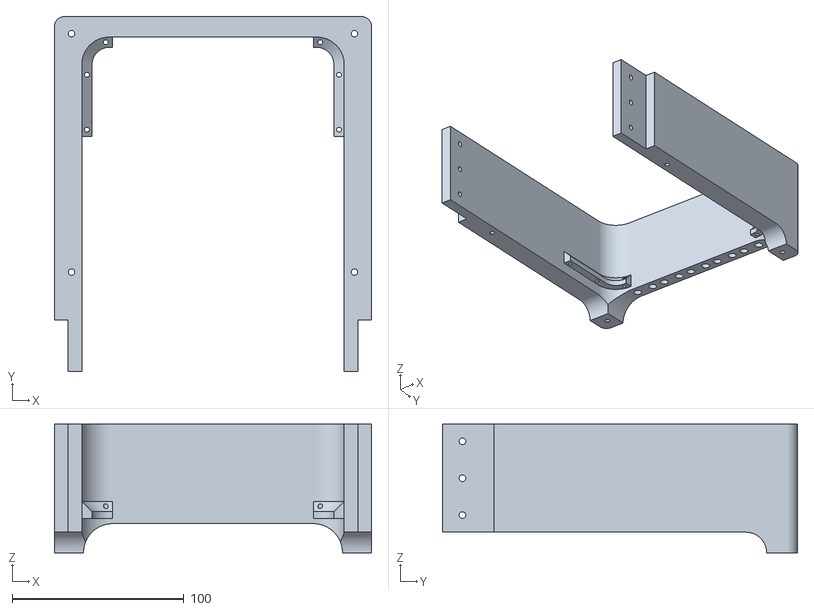
[picture p81: CAD file, 2020-06-08]
Base Stand - Case 3.0 and 5.0/Base Stand Rear V3_0 Standard_Tall_2pc.stl
185.0 x 207.0 x 75.0
