bgdog1/3dPrinterCase/Case - PRO V5.0 - 2 Piece/Lid Pro - Rear Standard 2 pc.stl

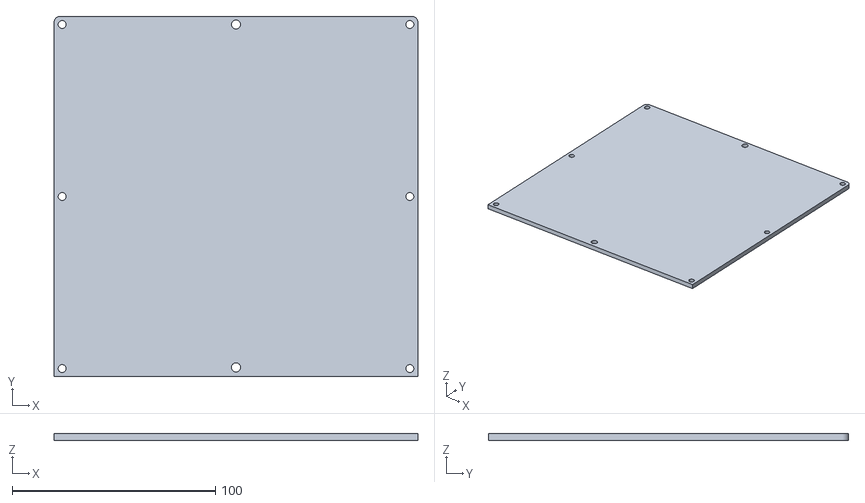
[picture p82: CAD file, 2020-09-07]
Case - PRO V5.0 - 2 Piece/Lid Pro - Rear Standard 2 pc.stl
179.0 x 177.2 x 3.20
