bgdog1/3dPrinterCase/Case - PRO V5.0/Lid - Pro.stl

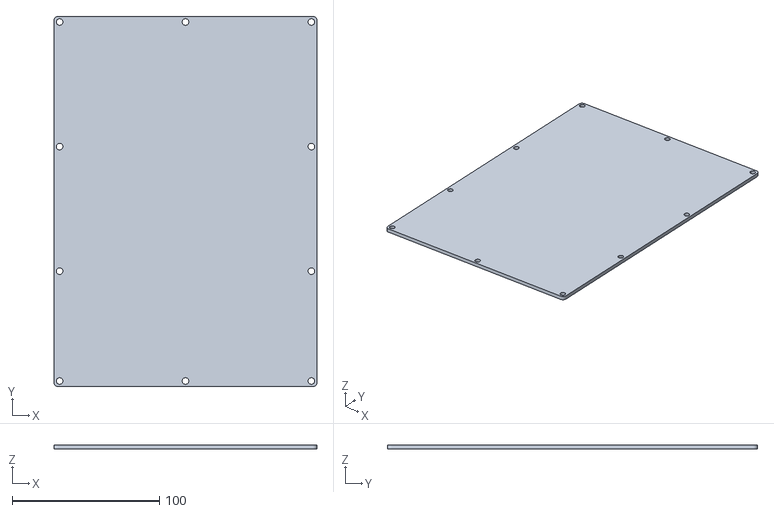
[picture p83: CAD file, 2020-03-22]
Case - PRO V5.0/Lid - Pro.stl
178.6 x 251.4 x 3.00
