bgdog1/3dPrinterCase/Case - Standard V5.x - 2 Piece/Base Front-Standard 2pc V2 wSwitch.stl

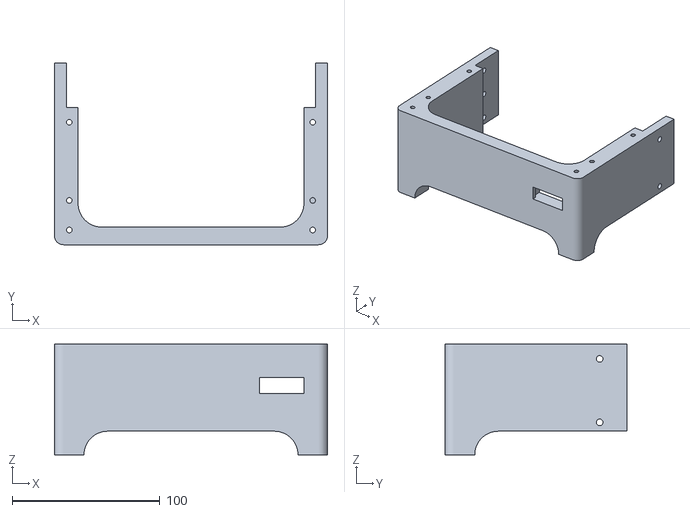
[picture p84: CAD file, 2023-01-15]
Case - Standard V5.x - 2 Piece/Base Front-Standard 2pc V2 wSwitch.stl
185.0 x 123.0 x 75.0
