bgdog1/3dPrinterCase/Case - XL Compact V5.X/Base Stand XL Compact - wSwitch.stl

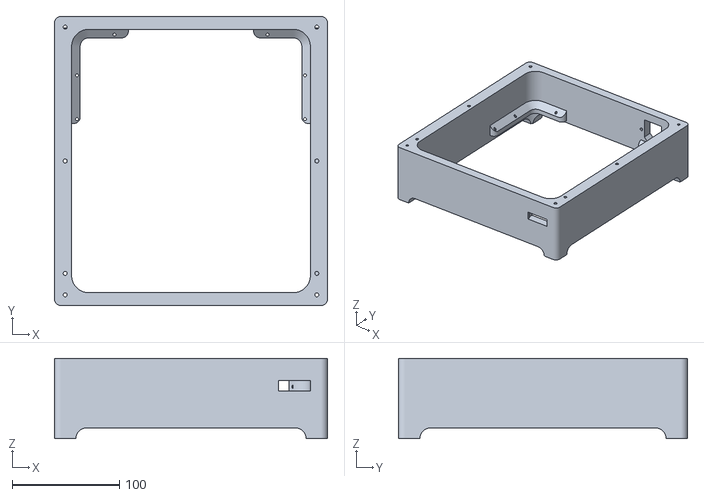
[picture p85: CAD file, 2020-08-29]
Case - XL Compact V5.X/Base Stand XL Compact - wSwitch.stl
255.0 x 270.0 x 75.0
