bgdog1/3dPrinterCase/Case - XL V5.X/Base Stand V5_0 XL - wSwitch.stl

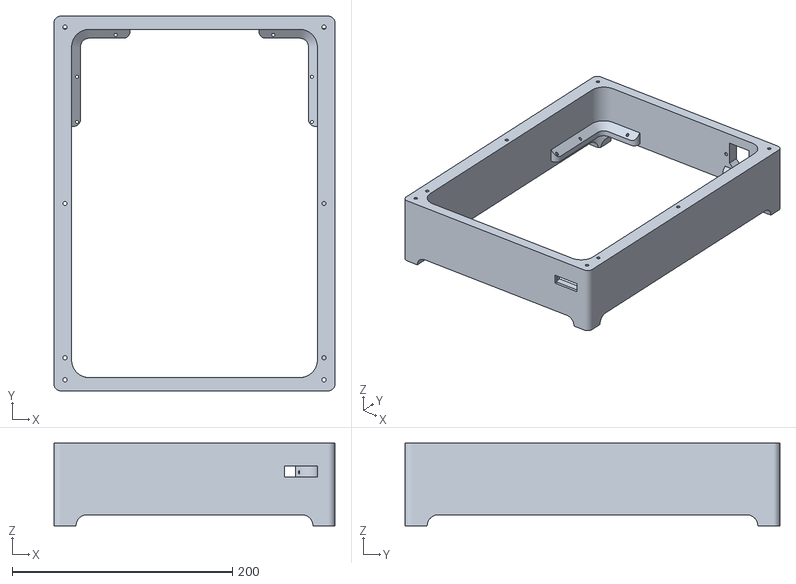
[picture p86: CAD file, 2020-09-06]
Case - XL V5.X/Base Stand V5_0 XL - wSwitch.stl
255.0 x 340.0 x 75.0
