bgdog1/3dPrinterCase/CPU Mounts/CPU Mount V2 - Orange Pi 3 LTS.stl

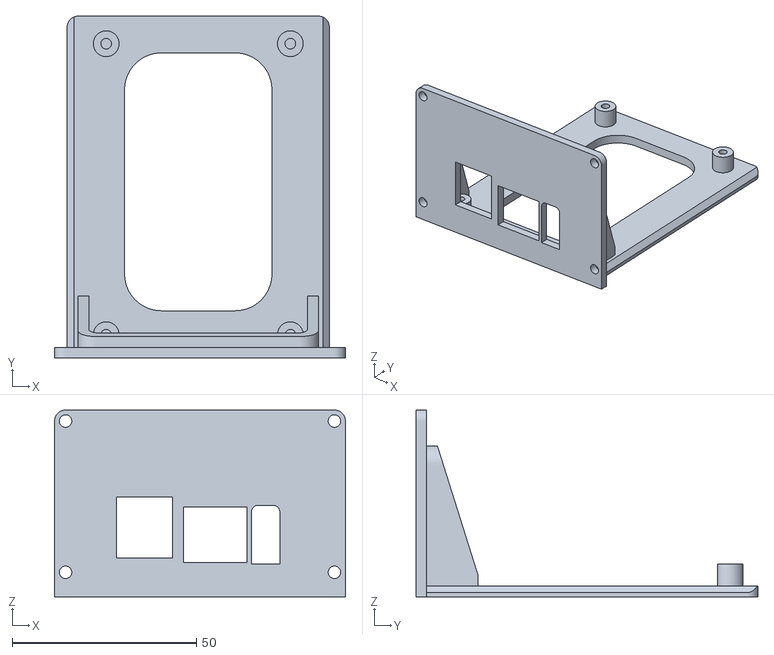
[picture p87: CAD file, 2023-04-07]
CPU Mounts/CPU Mount V2 - Orange Pi 3 LTS.stl
79.0 x 92.8 x 50.8
