bgdog1/3dPrinterCase/Display Mounts - Universal/Display Mount - RepRap12864 SD Access  Spacer.stl

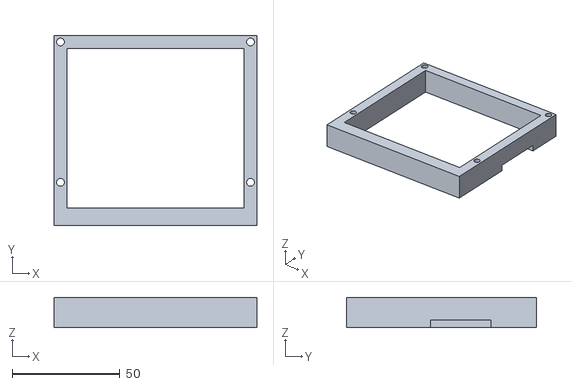
[picture p88: CAD file, 2020-07-26]
Display Mounts - Universal/Display Mount - RepRap12864 SD Access Spacer.stl
94.0 x 88.0 x 14.0
