bgdog1/3dPrinterCase/Display Mounts - XL/Display Mount XL - Blank.stl

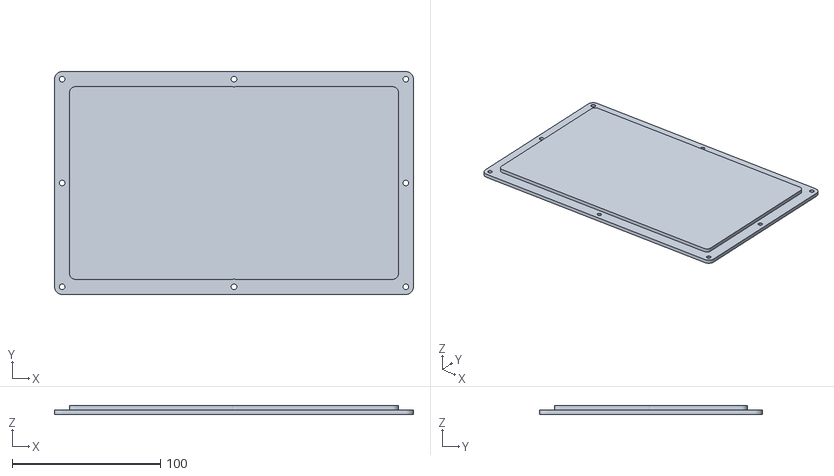
[picture p89: CAD file, 2020-09-06]
Display Mounts - XL/Display Mount XL - Blank.stl
242.5 x 150.5 x 6.00
