bgdog1/3dPrinterCase/Display Mounts/Display Mount - TFT70V30 SD Access Base.stl

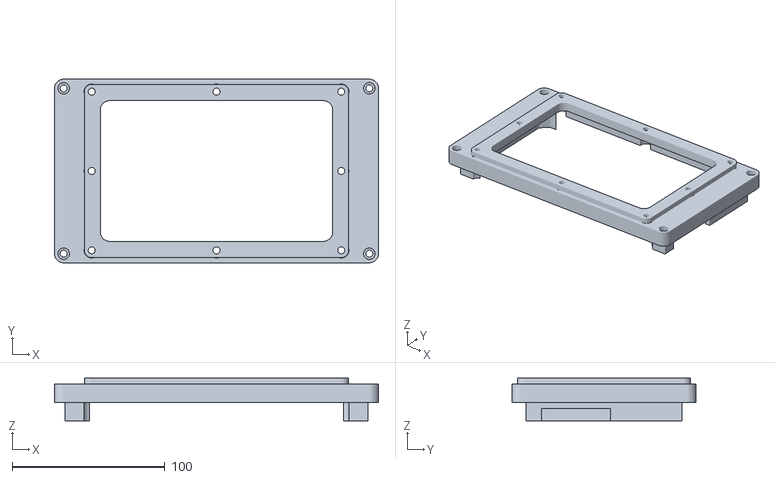
[picture p90: CAD file, 2020-08-16]
Display Mounts/Display Mount - TFT70V30 SD Access Base.stl
212.0 x 120.2 x 28.0
