bgdog1/3dPrinterCase/Power Panels - Case 3.0/Power Mount Panel Compact - IEC Connector.stl

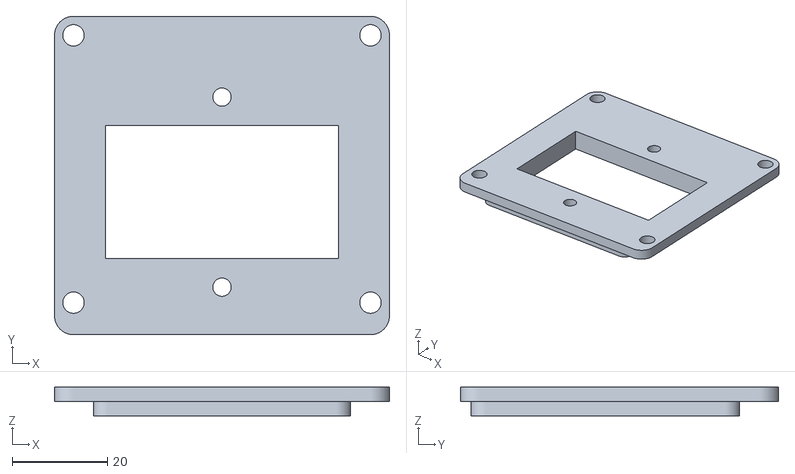
[picture p92: CAD file, 2020-03-22]
Power Panels - Case 3.0/Power Mount Panel Compact - IEC Connector.stl
70.5 x 67.0 x 6.00
