bgdog1/3dPrinterCase/Rear Fan Cover/Rear Fan External Cover 80mm.stl

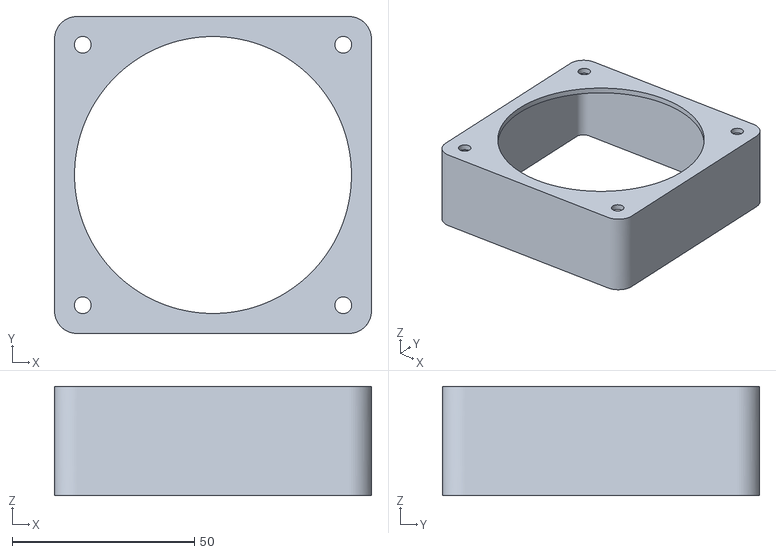
[picture p93: CAD file, 2020-03-29]
Rear Fan Cover/Rear Fan External Cover 80mm.stl
87.0 x 87.0 x 30.0
