bgdog1/3dPrinterCase/RPi Screen Mounts/RPi Screen Lid - Standard.stl

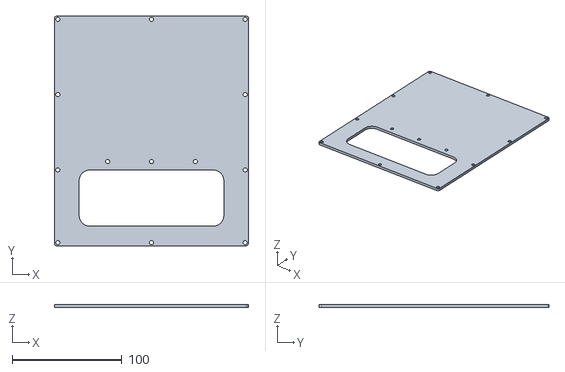
[picture p94: CAD file, 2021-04-14]
RPi Screen Mounts/RPi Screen Lid - Standard.stl
177.0 x 209.8 x 3.00
