bgdog1/3dPrinterCase/Base Stand - Case 3.0 and 5.0/Base Stand Front V3_0 Standard_Slim_2pc.stl

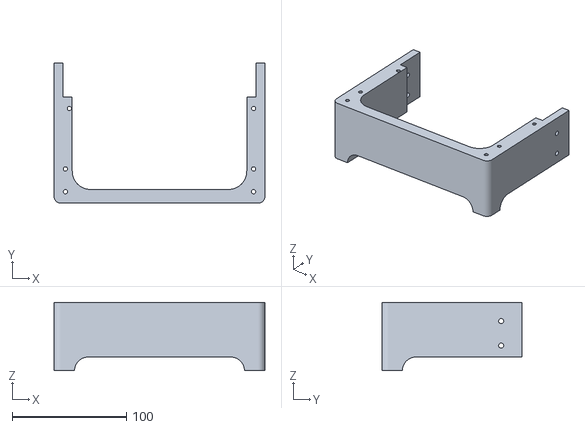
[picture p96: CAD file, 2020-06-08]
Base Stand - Case 3.0 and 5.0/Base Stand Front V3_0 Standard_Slim_2pc.stl
185.0 x 123.0 x 60.0
