bgdog1/3dPrinterCase/Case - PRO V5.0 - 2 Piece/Lid Pro _ Front Standard 2 pc.stl

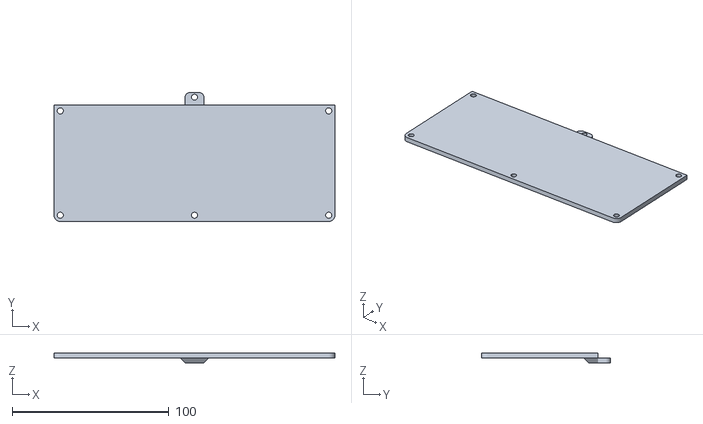
[picture p97: CAD file, 2020-09-07]
Case - PRO V5.0 - 2 Piece/Lid Pro _ Front Standard 2 pc.stl
179.0 x 82.2 x 6.20
