bgdog1/3dPrinterCase/Case - PRO V5.0/Base Stand Pro.stl

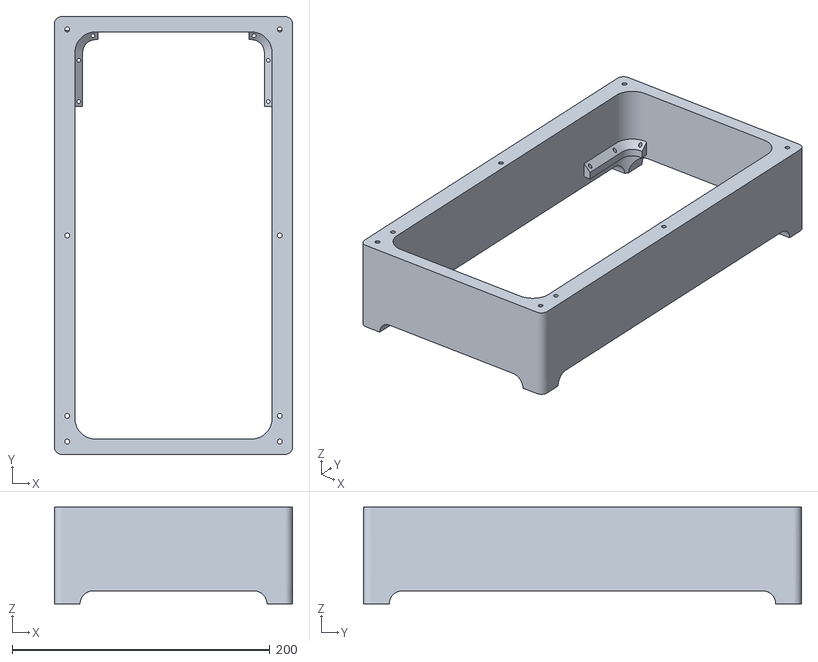
[picture p98: CAD file, 2020-03-22]
Case - PRO V5.0/Base Stand Pro.stl
185.0 x 340.0 x 75.0
