bgdog1/3dPrinterCase/Case - Standard V5.X - 2 Piece/Base Rear -Standard 2pc V2 wIEC Connector.stl

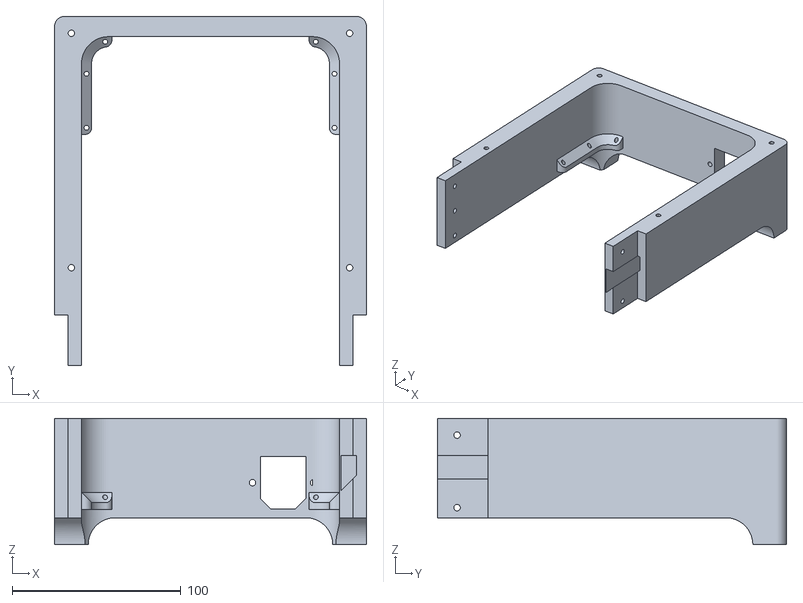
[picture p99: CAD file, 2022-03-13]
Case - Standard V5.X - 2 Piece/Base Rear -Standard 2pc V2 wIEC Connector.stl
185.0 x 207.0 x 75.0
