bgdog1/3dPrinterCase/Case - XL V5.X/Lid XL.stl

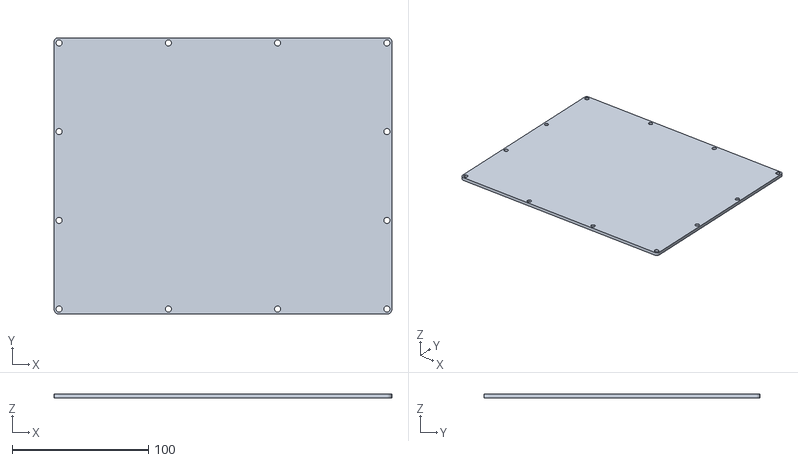
[picture p100: CAD file, 2020-09-01]
Case - XL V5.X/Lid XL.stl
248.5 x 203.1 x 3.20
