bgdog1/3dPrinterCase/CPU Mounts/CPU Mount V2 - RPi 3B+.stl

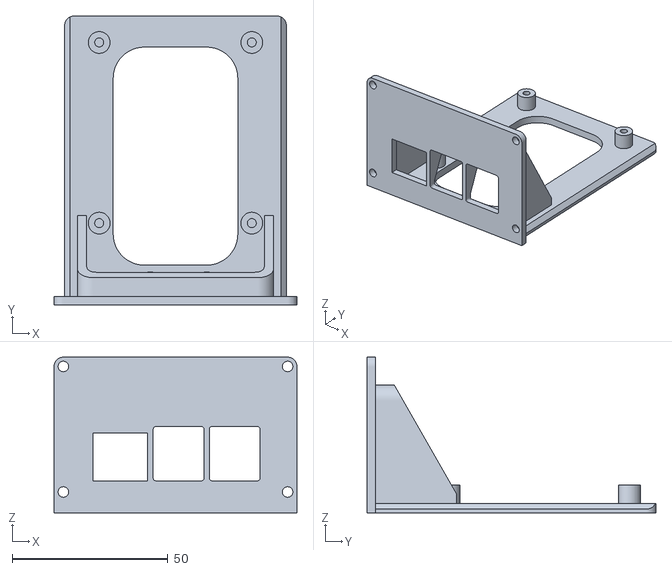
[picture p101: CAD file, 2023-01-29]
CPU Mounts/CPU Mount V2 - RPi 3B+.stl
78.0 x 92.8 x 50.0
