bgdog1/3dPrinterCase/Display Mounts - Universal/Display Mount - RepRap LCD12864 SD Access Cover.stl

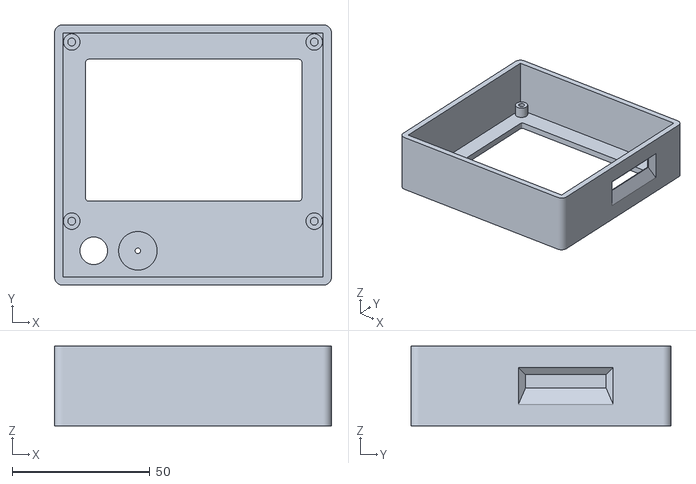
[picture p102: CAD file, 2020-07-26]
Display Mounts - Universal/Display Mount - RepRap LCD12864 SD Access Cover.stl
100.5 x 94.5 x 29.0
