bgdog1/3dPrinterCase/Display Mounts - XL/Display Mount XL - TFT70V30 SD Access Cover.stl

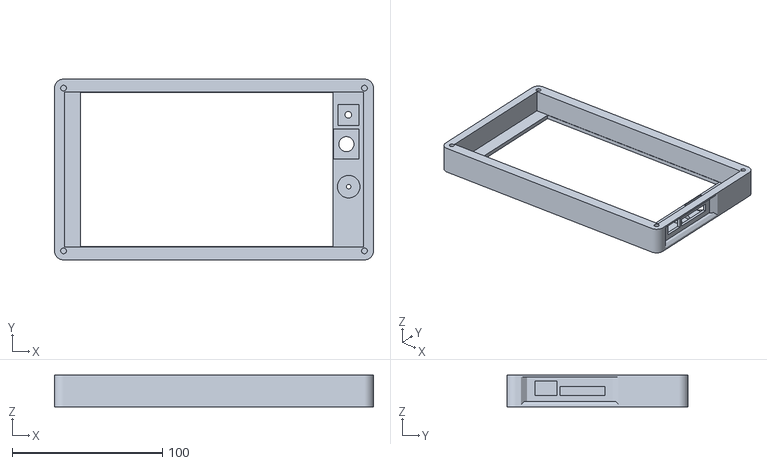
[picture p103: CAD file, 2020-09-06]
Display Mounts - XL/Display Mount XL - TFT70V30 SD Access Cover.stl
212.0 x 120.2 x 21.0
