bgdog1/3dPrinterCase/Fan Mounts - Case 3.0 and 5.0/Fan Mount - Dual 4020mm Dual Tray.stl

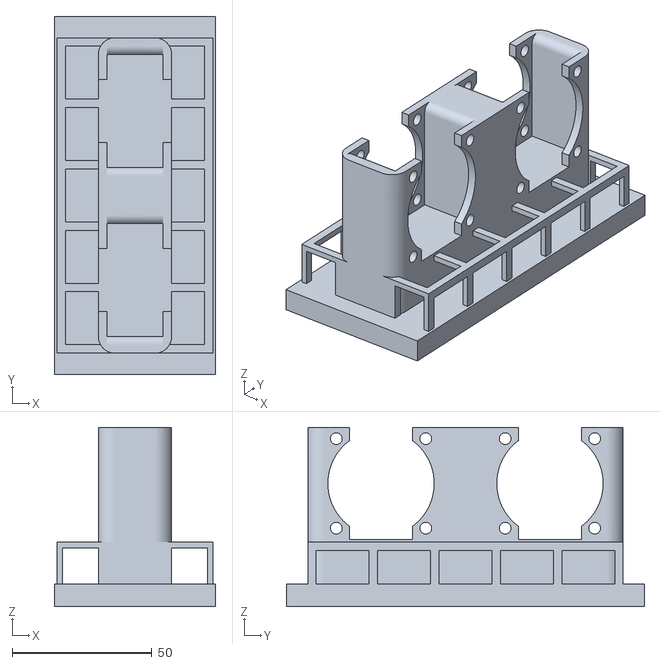
[picture p104: CAD file, 2020-03-29]
Fan Mounts - Case 3.0 and 5.0/Fan Mount - Dual 4020mm Dual Tray.stl
57.7 x 128.0 x 64.0
