bgdog1/3dPrinterCase/Front Vents - Universal/Front Vent -  BTT.stl

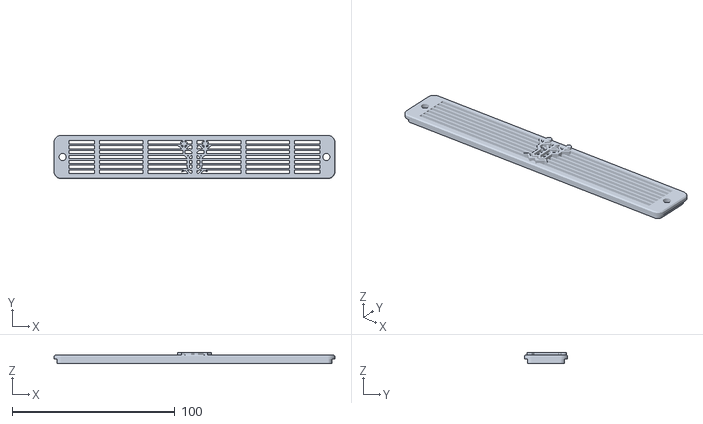
[picture p105: CAD file, 2020-04-05]
Front Vents - Universal/Front Vent - BTT.stl
172.6 x 26.6 x 6.80
