bgdog1/3dPrinterCase/Power Panels - Case 3.0/Power Mount Panel - BLANK.stl

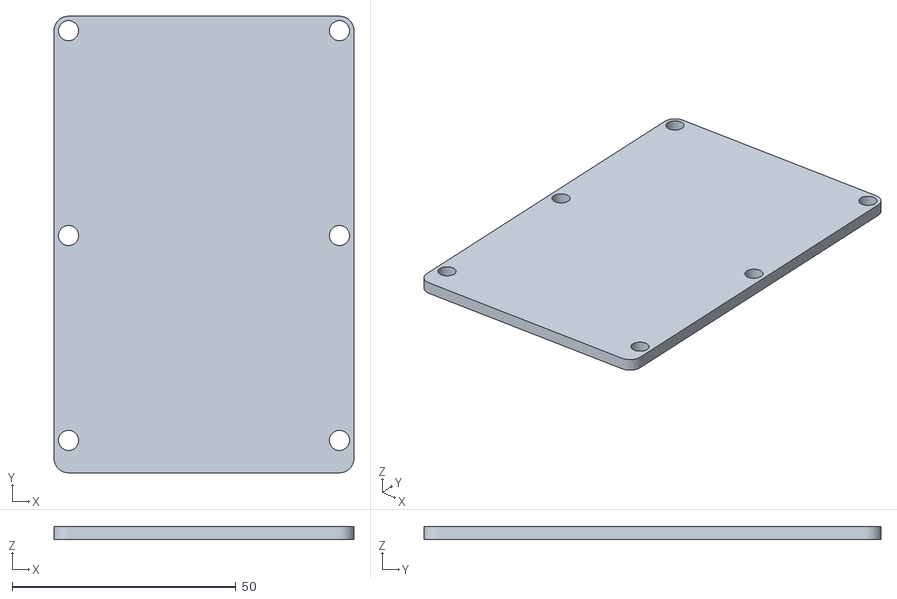
[picture p106: CAD file, 2020-03-22]
Power Panels - Case 3.0/Power Mount Panel - BLANK.stl
67.0 x 102.0 x 3.00
