bgdog1/3dPrinterCase/Rear Fan Cover/Rear Fan External Cover 90mm.stl

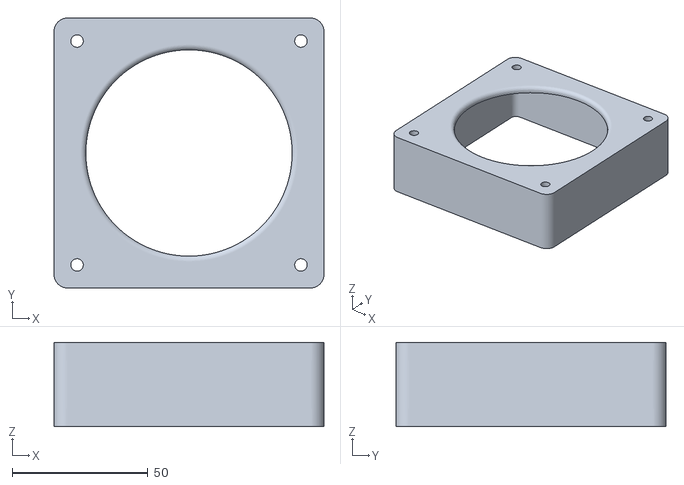
[picture p107: CAD file, 2020-03-28]
Rear Fan Cover/Rear Fan External Cover 90mm.stl
99.5 x 99.5 x 31.0
