bgdog1/3dPrinterCase/Rear Mount Ender 3 Case V3.0/E3 Pro Rear Case V5 - Center Lid.stl

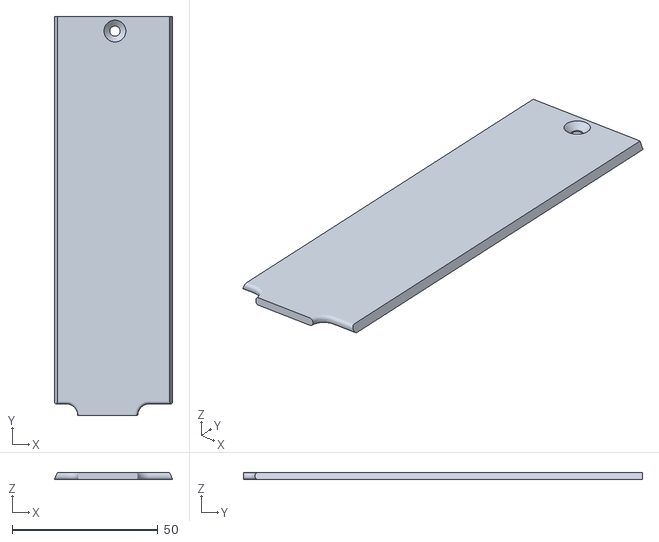
[picture p108: CAD file, 2023-02-08]
Rear Mount Ender 3 Case V3.0/E3 Pro Rear Case V5 - Center Lid.stl
40.6 x 137.0 x 2.41
