bgdog1/3dPrinterCase/Rear Panels/Rear Panel - 92mm Fan.stl

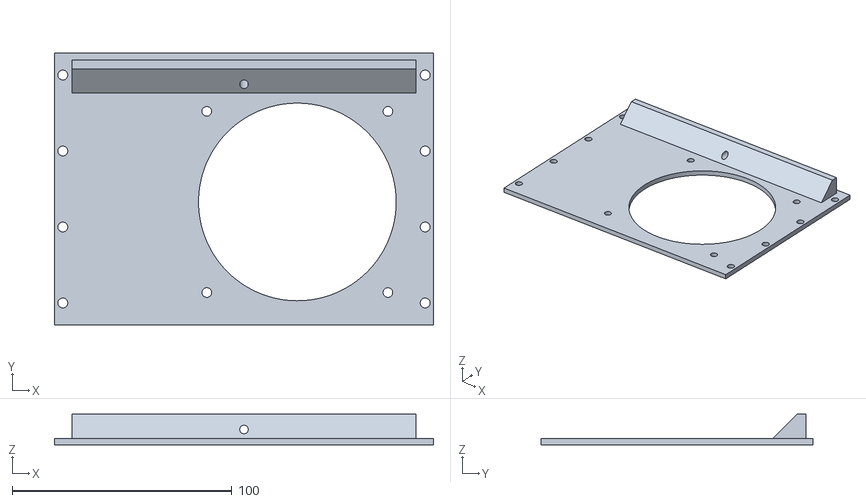
[picture p109: CAD file, 2020-10-25]
Rear Panels/Rear Panel - 92mm Fan.stl
172.6 x 123.8 x 14.0
