bgdog1/3dPrinterCase/RPi Screen Mounts/RPi Screen Lid - Pro Standard.stl

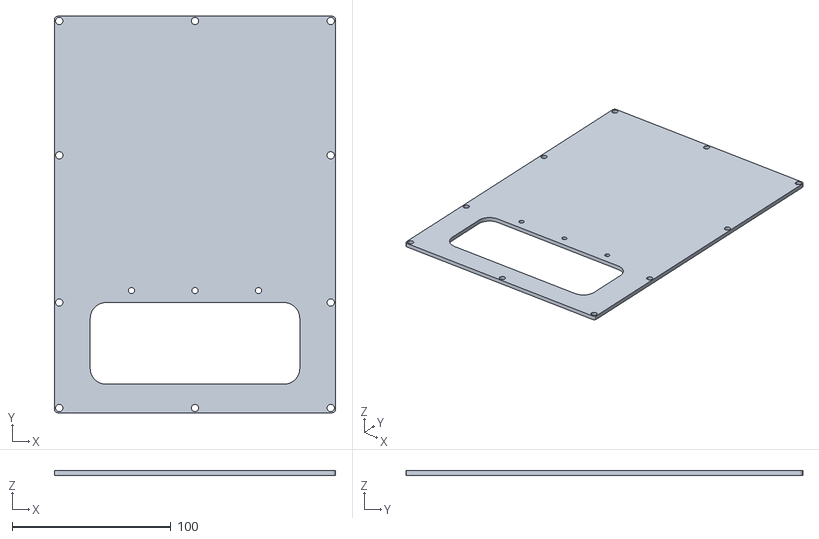
[picture p110: CAD file, 2021-04-14]
RPi Screen Mounts/RPi Screen Lid - Pro Standard.stl
177.0 x 249.8 x 3.00
