bgdog1/3dPrinterCase/Upper Level Mounts - Case 4.0 and up/Upper Level Mount - Blank.stl

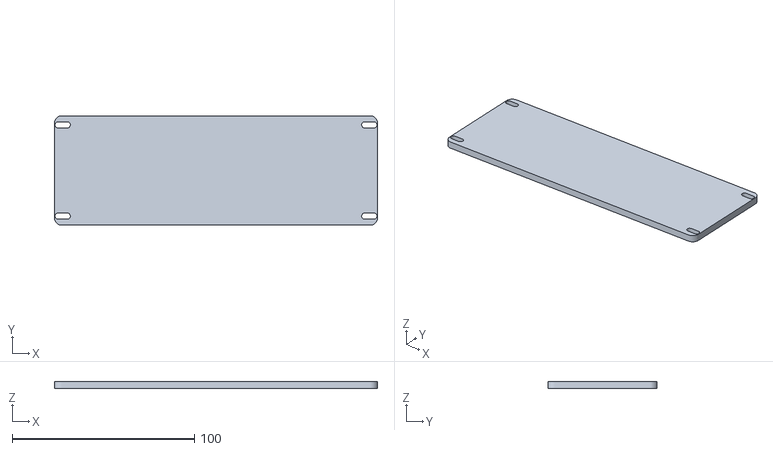
[picture p111: CAD file, 2020-06-04]
Upper Level Mounts - Case 4.0 and up/Upper Level Mount - Blank.stl
177.0 x 60.0 x 4.00
