bgdog1/3dPrinterCase/Base Stand - Case 3.0 and 5.0/Base Stand V3_0 - Standard_Tall.stl

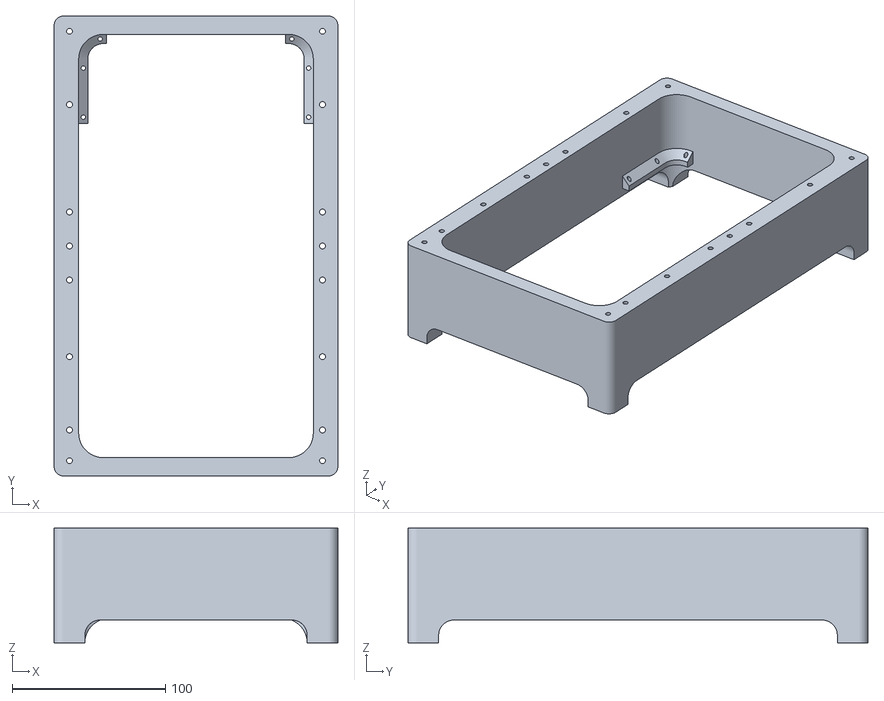
[picture p112: CAD file, 2020-04-29]
Base Stand - Case 3.0 and 5.0/Base Stand V3_0 - Standard_Tall.stl
185.0 x 300.0 x 75.0
