bgdog1/3dPrinterCase/Display Mounts - XL/Display Mount XL - TFT70V30 SD Access Base.stl

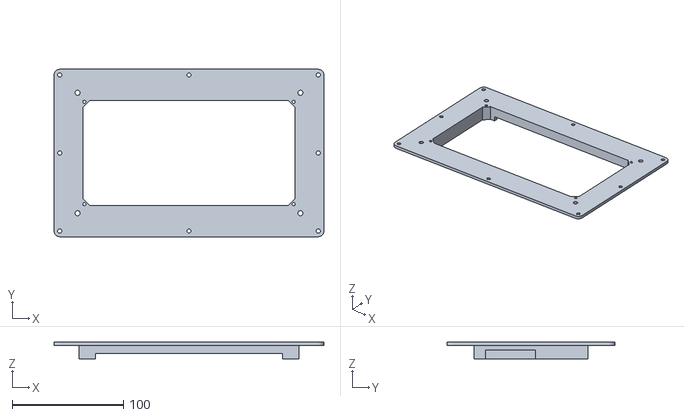
[picture p113: CAD file, 2020-09-06]
Display Mounts - XL/Display Mount XL - TFT70V30 SD Access Base.stl
242.5 x 150.5 x 15.0
