bgdog1/3dPrinterCase/Display Mounts/Display Mount PRO - LCD12864.stl

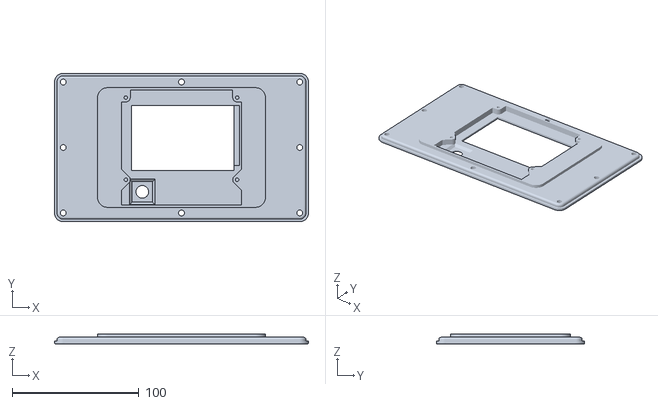
[picture p114: CAD file, 2020-03-23]
Display Mounts/Display Mount PRO - LCD12864.stl
200.8 x 117.3 x 8.00
