bgdog1/3dPrinterCase/Fan Mounts - Case 3.0 and 5.0/Fan Mount - Triple 4020mm Dual Wire Tray.stl

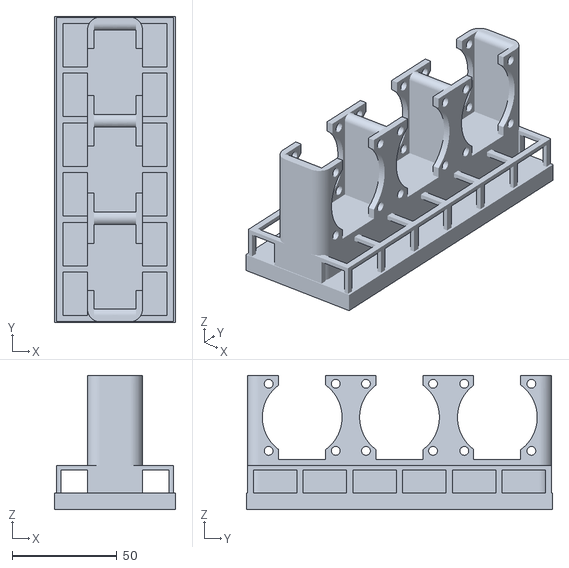
[picture p115: CAD file, 2020-03-29]
Fan Mounts - Case 3.0 and 5.0/Fan Mount - Triple 4020mm Dual Wire Tray.stl
57.7 x 146.0 x 64.0
