bgdog1/3dPrinterCase/Front Vents - Universal/Front Vent -  Bowtie.stl

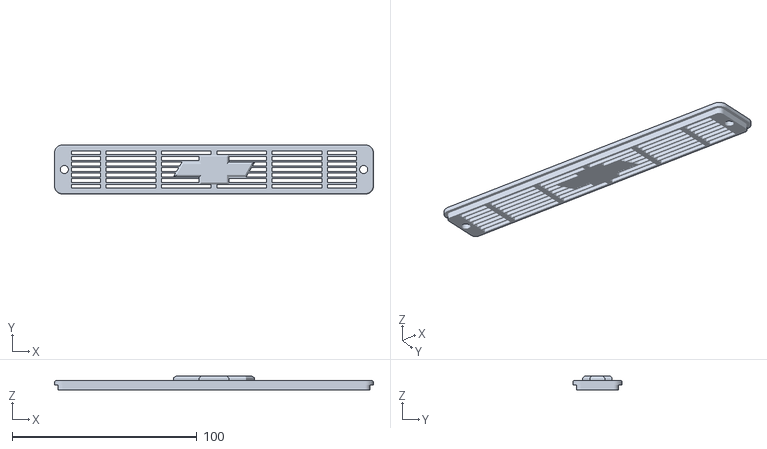
[picture p116: CAD file, 2020-04-05]
Front Vents - Universal/Front Vent - Bowtie.stl
172.6 x 26.6 x 7.60
