bgdog1/3dPrinterCase/Rear Panels/Rear Panel - 100mm Fan.stl

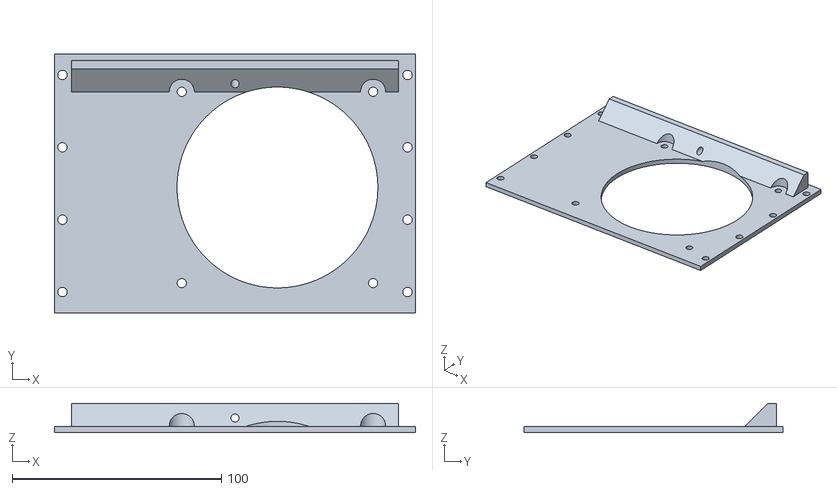
[picture p117: CAD file, 2020-09-06]
Rear Panels/Rear Panel - 100mm Fan.stl
172.6 x 123.8 x 14.0
