bgdog1/3dPrinterCase/RPi Screen Mounts/XL RPi Screen Mount Lid.stl

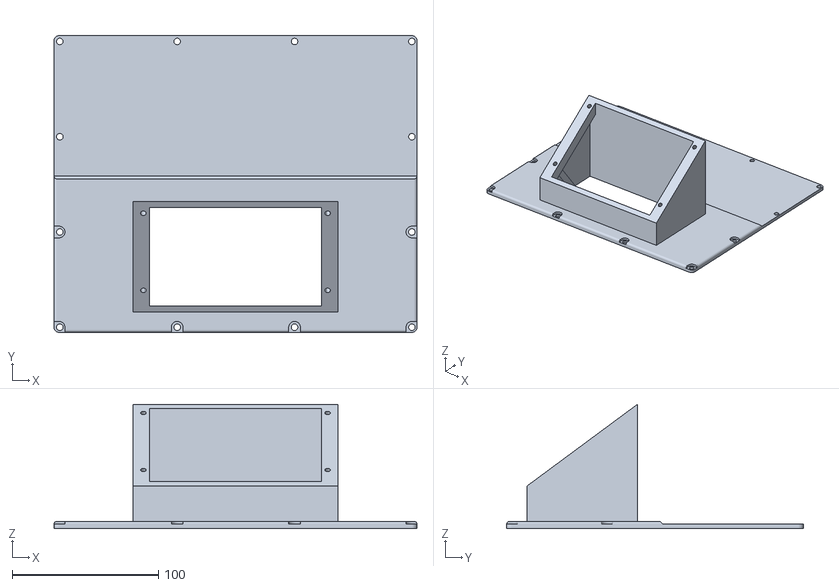
[picture p118: CAD file, 2020-10-04]
RPi Screen Mounts/XL RPi Screen Mount Lid.stl
248.5 x 203.1 x 85.0
