bgdog1/3dPrinterCase/Upper Level Mounts - Case 4.0 and up/Upper Level Mount - 2Bucks.stl

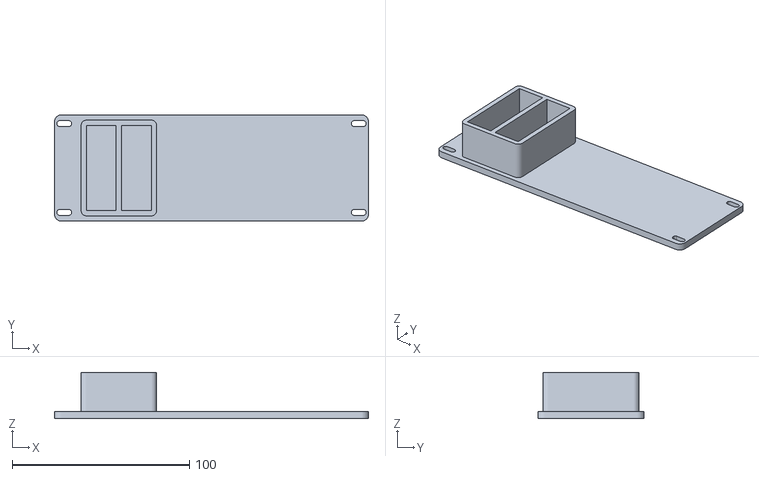
[picture p119: CAD file, 2020-06-04]
Upper Level Mounts - Case 4.0 and up/Upper Level Mount - 2Bucks.stl
177.0 x 60.0 x 26.0
