bgdog1/3dPrinterCase/Base Stand - Case 3.0 and 5.0/Base Stand V3_0 - Standard_Slim.stl

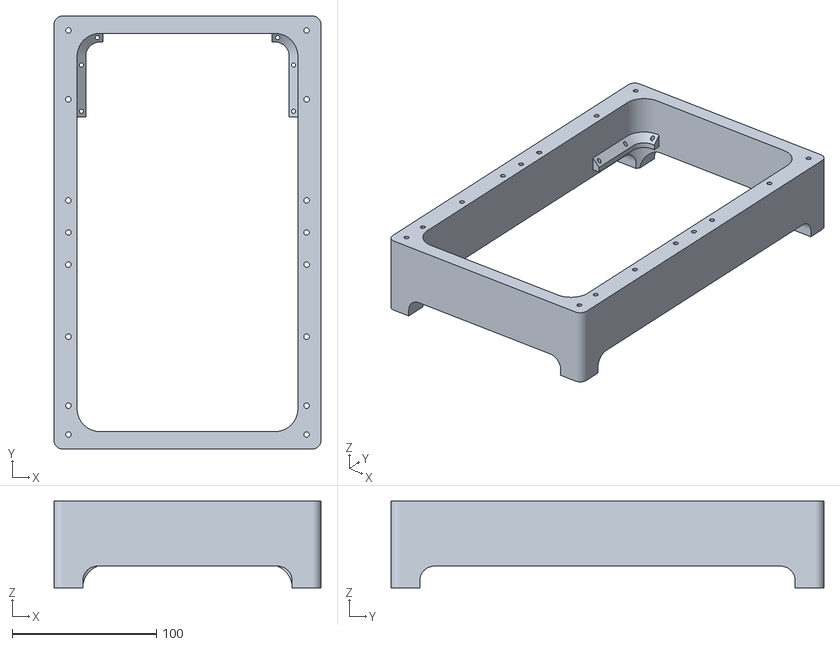
[picture p120: CAD file, 2020-04-29]
Base Stand - Case 3.0 and 5.0/Base Stand V3_0 - Standard_Slim.stl
185.0 x 300.0 x 60.0
