bgdog1/3dPrinterCase/Case - Standard V5.X - 2 Piece/PSU Terminal Cover V2.stl

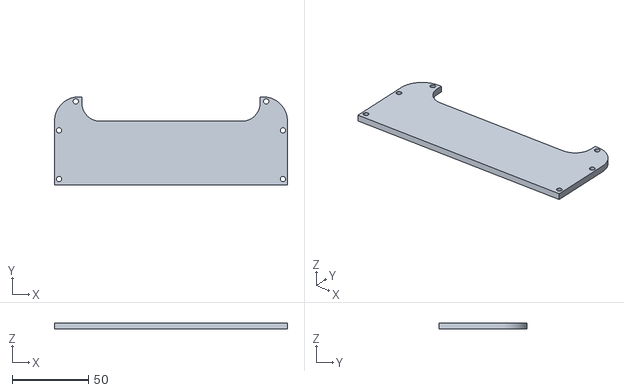
[picture p121: CAD file, 2020-09-20]
Case - Standard V5.X - 2 Piece/PSU Terminal Cover V2.stl
153.0 x 58.0 x 4.00
