bgdog1/3dPrinterCase/CPU Mounts/CPU Mount - Orange Pi Lite.stl

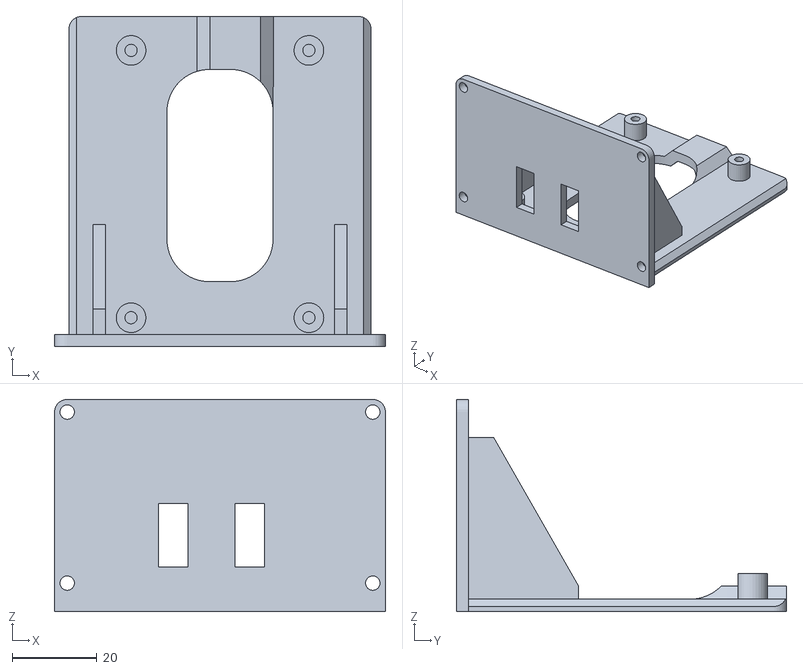
[picture p122: CAD file, 2020-06-05]
CPU Mounts/CPU Mount - Orange Pi Lite.stl
78.0 x 77.8 x 50.0
