bgdog1/3dPrinterCase/Display Mounts - Universal/Display Mount - TFT24V1_1 Spacer SD Access.stl

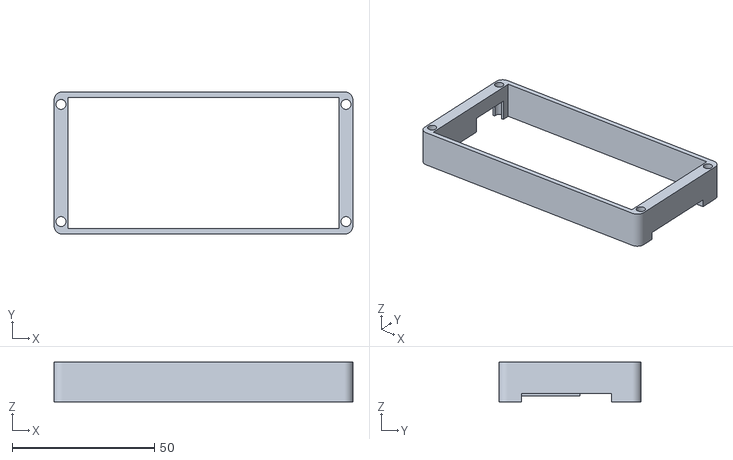
[picture p123: CAD file, 2020-06-08]
Display Mounts - Universal/Display Mount - TFT24V1_1 Spacer SD Access.stl
105.0 x 50.0 x 14.0
