bgdog1/3dPrinterCase/Display Mounts/Display Mount PRO - Blank.stl

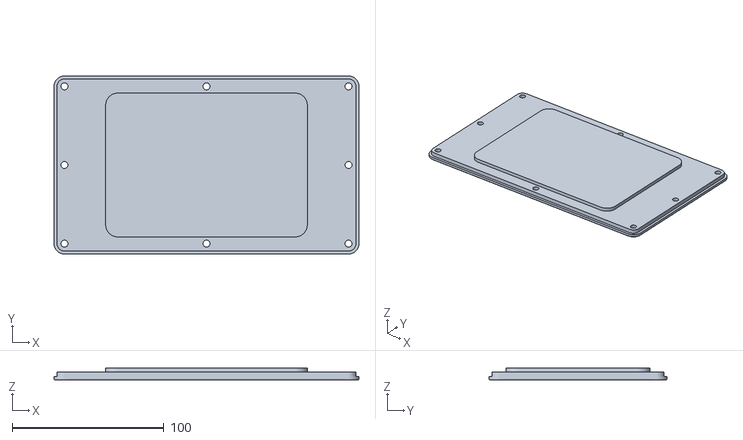
[picture p124: CAD file, 2020-03-23]
Display Mounts/Display Mount PRO - Blank.stl
200.8 x 117.3 x 8.00
