bgdog1/3dPrinterCase/Fan Mounts - Case 3.0 and 5.0/Rear Fan Mount - External Base 92mm.stl

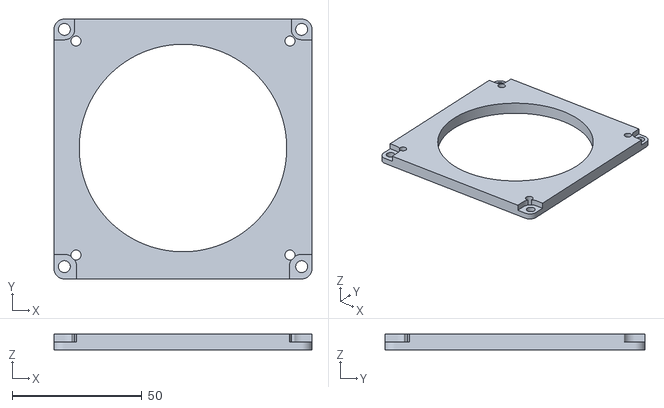
[picture p125: CAD file, 2020-03-29]
Fan Mounts - Case 3.0 and 5.0/Rear Fan Mount - External Base 92mm.stl
99.5 x 100.2 x 6.00
