bgdog1/3dPrinterCase/Rear Mount Ender 3 Case V3.0/E3 Rear Case V5 - Drag Chain Adapter.stl

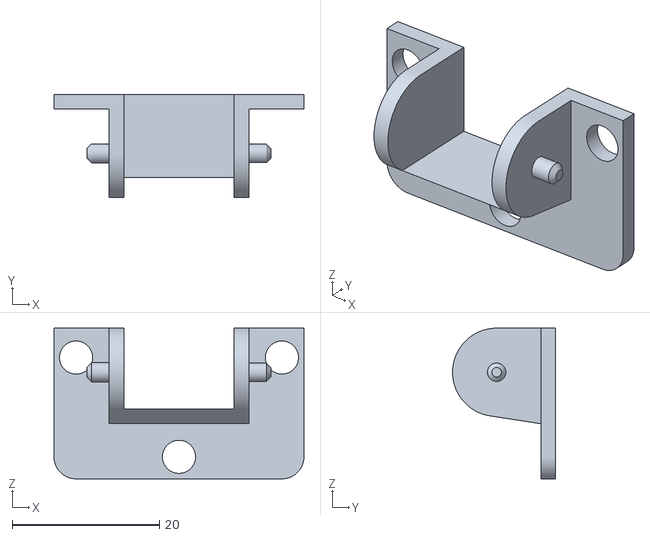
[picture p126: CAD file, 2023-02-08]
Rear Mount Ender 3 Case V3.0/E3 Rear Case V5 - Drag Chain Adapter.stl
34.0 x 14.0 x 20.5
